bartpleiter/FPGC5/PCB/FPGC5IOboard/mini-din-6p-1.snapshot.2/Mini-DIN-6P.png

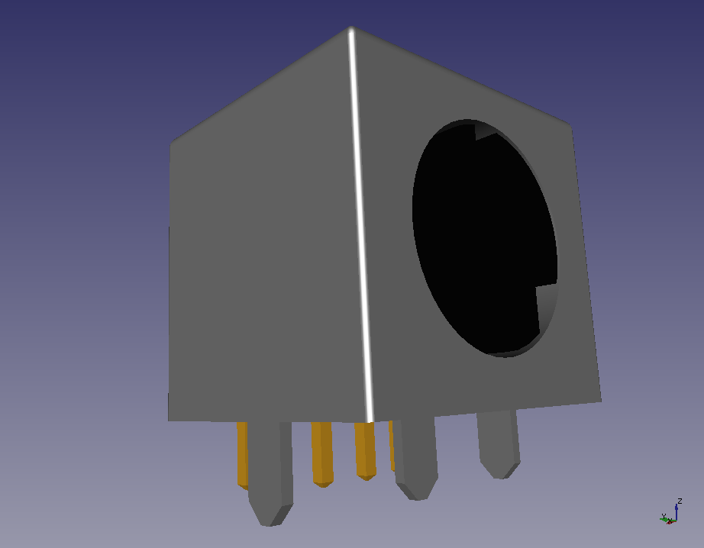
PCB/FPGC5IOboard/mini-din-6p-1.snapshot.2/Mini-DIN-6P.png
