bartpleiter/FPGC5/PCB/FPGC5IOboard/renders/FPGC4IOboardV2Bottom.png

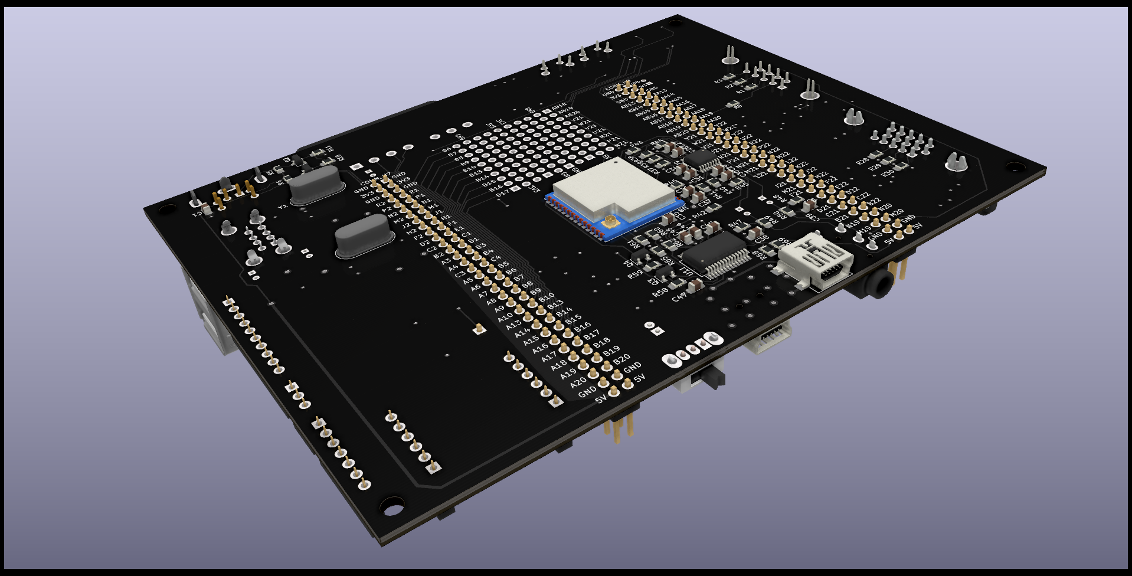
PCB/FPGC5IOboard/renders/FPGC4IOboardV2Bottom.png
