bartpleiter/FPGC5/PCB/FPGC5IOboard/renders/FPGC4IOboardV2BottomCloseUp.png

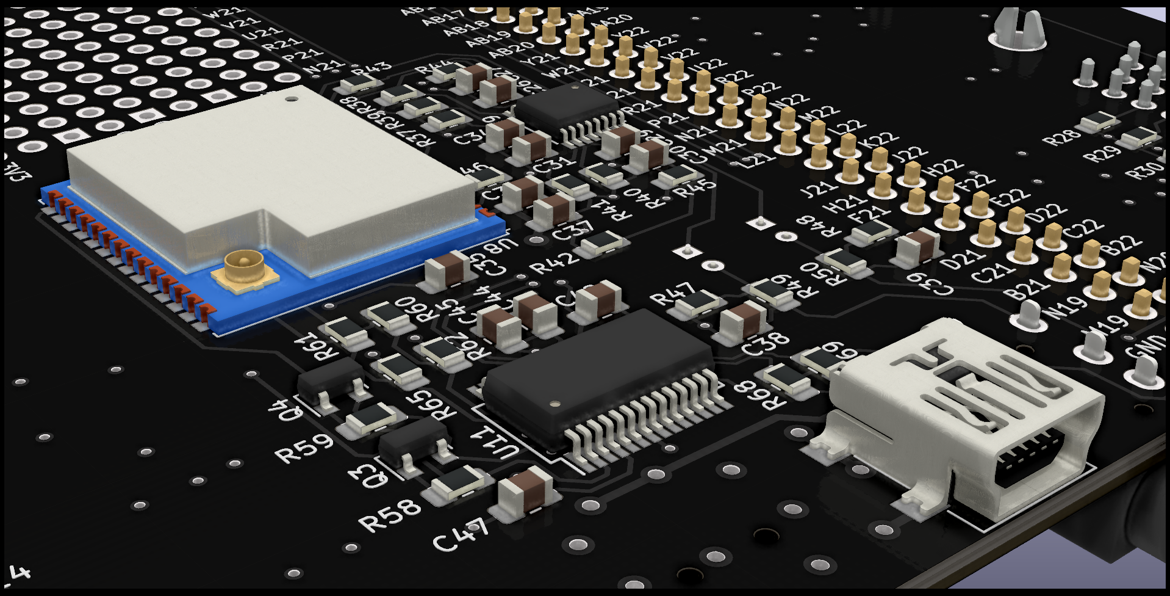
PCB/FPGC5IOboard/renders/FPGC4IOboardV2BottomCloseUp.png
