bartpleiter/FPGC5/PCB/FPGC5IOboard/renders/FPGC4IOboardV2FrontCloseUp.png

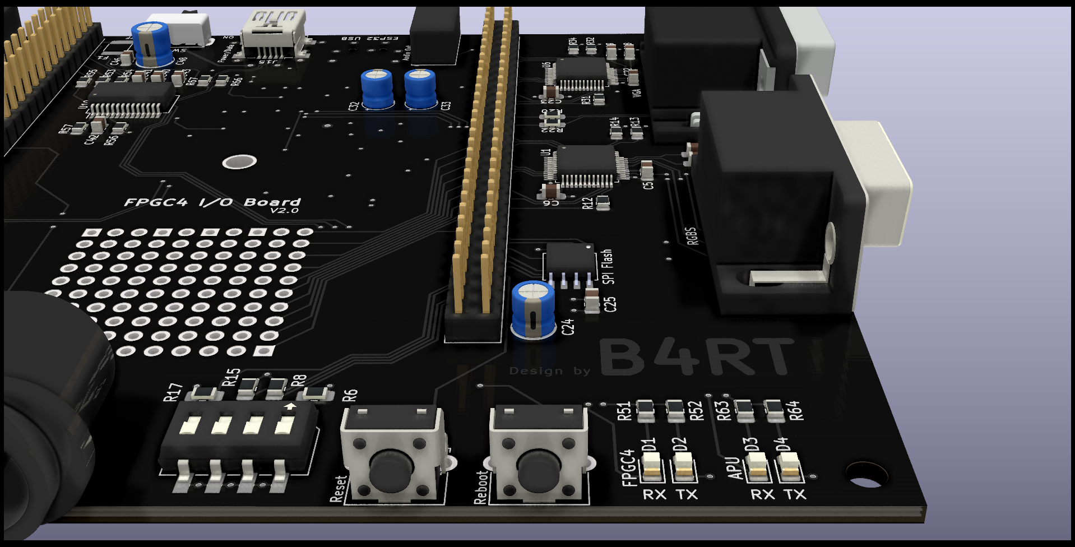
PCB/FPGC5IOboard/renders/FPGC4IOboardV2FrontCloseUp.png
