bartpleiter/FPGC5/PCB/FPGC5IOboard/renders/FPGC4IOboardV2Top.png

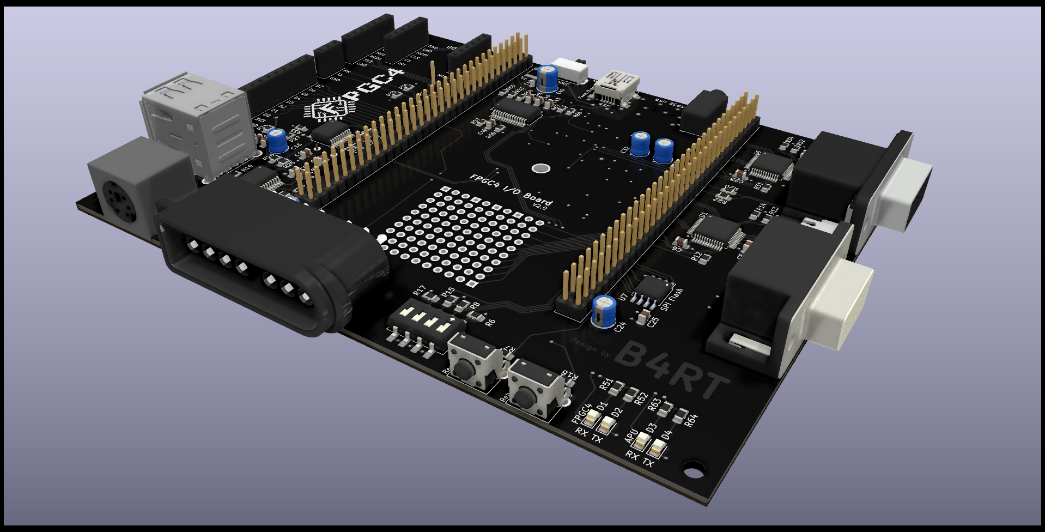
PCB/FPGC5IOboard/renders/FPGC4IOboardV2Top.png
