bartpleiter/FPGC5/PCB/FPGC5IOboard/3.5mm3D/FC68128.step

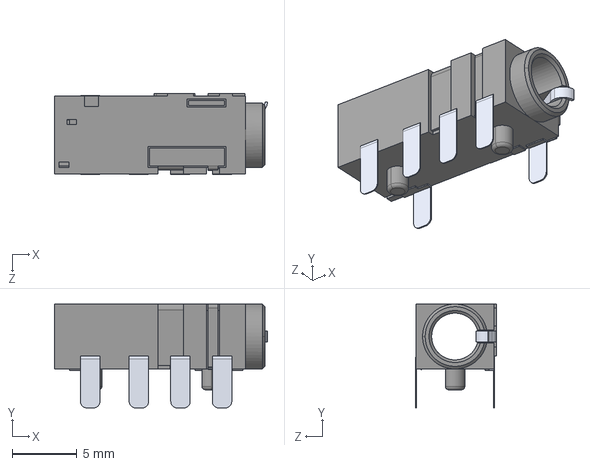
[picture p31: CAD file, 2021-06-23]
PCB/FPGC5IOboard/3.5mm3D/FC68128.step
16.4 x 8.00 x 6.25 mm
