bartpleiter/FPGC5/BCC/bcc.c

/*
Copyright (c) 2021, b4rt-dev
Copyright (c) 2012-2020, Alexey Frunze
All rights reserved.

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
1. Redistributions of source code must retain the above copyright notice, this
   list of conditions and the following disclaimer.
2. Redistributions in binary form must reproduce the above copyright notice,
   this list of conditions and the following disclaimer in the documentation
   and/or other materials provided with the distribution.

THIS SOFTWARE IS PROVIDED BY THE COPYRIGHT HOLDERS AND CONTRIBUTORS "AS IS" AND
ANY EXPRESS OR IMPLIED WARRANTIES, INCLUDING, BUT NOT LIMITED TO, THE IMPLIED
WARRANTIES OF MERCHANTABILITY AND FITNESS FOR A PARTICULAR PURPOSE ARE
DISCLAIMED. IN NO EVENT SHALL THE COPYRIGHT OWNER OR CONTRIBUTORS BE LIABLE FOR
ANY DIRECT, INDIRECT, INCIDENTAL, SPECIAL, EXEMPLARY, OR CONSEQUENTIAL DAMAGES
(INCLUDING, BUT NOT LIMITED TO, PROCUREMENT OF SUBSTITUTE GOODS OR SERVICES;
LOSS OF USE, DATA, OR PROFITS; OR BUSINESS INTERRUPTION) HOWEVER CAUSED AND
ON ANY THEORY OF LIABILITY, WHETHER IN CONTRACT, STRICT LIABILITY, OR TORT
(INCLUDING NEGLIGENCE OR OTHERWISE) ARISING IN ANY WAY OUT OF THE USE OF THIS
SOFTWARE, EVEN IF ADVISED OF THE POSSIBILITY OF SUCH DAMAGE.
*/

/*****************************************************************************/
/*                                                                           */
/*                           BCC (B322 C Compiler)                           */
/*                                                                           */
/*                           C compiler for B322                             */
/*                                                                           */
/*                            Based on SmallerC:                             */
/*                 A simple and small single-pass C compiler                 */
/*                                                                           */
/*                                Main file                                  */
/*                                                                           */
/*****************************************************************************/

// NOTE: still has a lot of extras in it that are not needed
//  only the "MIPS" part is needed with no extras

// Making most functions static helps with code optimization,
// use that to further reduce compiler's code size on RetroBSD.
#ifndef STATIC
#define STATIC
#else
#undef STATIC
#define STATIC static
#endif

#define NO_EXTRAS
#define CAN_COMPILE_32BIT
#define MIPS
#define B322

#ifdef NO_EXTRAS
#define NO_PPACK
#define NO_TYPEDEF_ENUM
#define NO_FUNC_
#define NO_EXTRA_WARNS
#define NO_FOR_DECL
#define NO_STRUCT_BY_VAL
#define NO_FP
#define NO_WCHAR
#endif

#ifndef __SMALLER_C__

//#include <limits.h>
#define CHAR_BIT        8
#define UINT_MAX        4294967295U
#define INT_MIN         -2147483648

//#include <ctype.h>
// isalpha
// isalnum
// isdigit

//#include <string.h>
// memmove
// strchr
// strcat
// strlen
// memcpy
// strncmp

#include <stdarg.h> // only used for printf related stuff and warnings/errors. Should be able to remove by replacing ALL(...) occurrences with a normal print function
#include <stdlib.h>
#include <stdio.h> // I/O functions

//#if UINT_MAX >= 0xFFFFFFFF
//#define CAN_COMPILE_32BIT
//#endif

#else // #ifndef __SMALLER_C__

#define NULL 0
#define size_t unsigned int

#define CHAR_BIT (8)

#ifdef __SMALLER_C_SCHAR__
#define CHAR_MIN (-128)
#define CHAR_MAX (127)
#endif
#ifdef __SMALLER_C_UCHAR__
#define CHAR_MIN (0)
#define CHAR_MAX (255)
#endif

#ifndef __SMALLER_C_SCHAR__
#ifndef __SMALLER_C_UCHAR__
#error __SMALLER_C_SCHAR__ or __SMALLER_C_UCHAR__ must be defined
#endif
#endif

#ifdef __SMALLER_C_16__
#define INT_MAX (32767)
#define INT_MIN (-32767-1)
#define UINT_MAX (65535u)
#define UINT_MIN (0u)
#endif
#ifdef __SMALLER_C_32__
#define INT_MAX (2147483647)
#define INT_MIN (-2147483647-1)
#define UINT_MAX (4294967295u)
#define UINT_MIN (0u)
//#define CAN_COMPILE_32BIT
#endif

#ifndef __SMALLER_C_16__
#ifndef __SMALLER_C_32__
#error __SMALLER_C_16__ or __SMALLER_C_32__ must be defined
#endif
#endif

#define EXIT_FAILURE 1

void exit(int);
int atoi(char*);

size_t strlen(char*);
char* strcpy(char*, char*);
char* strchr(char*, int);
int strcmp(char*, char*);
int strncmp(char*, char*, size_t);
void* memmove(void*, void*, size_t);
void* memcpy(void*, void*, size_t);
void* memset(void*, int, size_t);
int memcmp(void*, void*, size_t);

int isspace(int);
int isdigit(int);
int isalpha(int);
int isalnum(int);

#define FILE void
#define EOF (-1)
FILE* fopen(char*, char*);
int fclose(FILE*);
int putchar(int);
int fputc(int, FILE*);
int fgetc(FILE*);
int puts(char*);
int fputs(char*, FILE*);
int sprintf(char*, char*, ...);
//int vsprintf(char*, char*, va_list);
int vsprintf(char*, char*, void*);
int printf(char*, ...);
int fprintf(FILE*, char*, ...);
//int vprintf(char*, va_list);
int vprintf(char*, void*);
//int vfprintf(FILE*, char*, va_list);
int vfprintf(FILE*, char*, void*);
struct fpos_t_
{
  union
  {
    unsigned short halves[2]; // for 16-bit memory models without 32-bit longs
    int align; // for alignment on machine word boundary
  } u;
}; // keep in sync with stdio.h !!!
#define fpos_t struct fpos_t_
int fgetpos(FILE*, fpos_t*);
int fsetpos(FILE*, fpos_t*);

#endif // #ifndef __SMALLER_C__

// Floating point requires 32 bits
#ifndef CAN_COMPILE_32BIT
#ifndef NO_FP
#define NO_FP
#endif
#endif

////////////////////////////////////////////////////////////////////////////////

// all public macros

#ifndef MAX_IDENT_LEN
#define MAX_IDENT_LEN        63
#endif

#ifndef MAX_STRING_LEN
#define MAX_STRING_LEN       255
#endif
#define MAX_CHAR_QUEUE_LEN   (MAX_STRING_LEN + 1)

#ifndef MAX_MACRO_TABLE_LEN
#define MAX_MACRO_TABLE_LEN  (8192+1024)
#endif

#ifndef MAX_IDENT_TABLE_LEN
#define MAX_IDENT_TABLE_LEN  (8192+1024+512) // must be greater than MAX_IDENT_LEN
#endif

#ifndef SYNTAX_STACK_MAX
#define SYNTAX_STACK_MAX (4096+1024)
#endif

#ifndef MAX_FILE_NAME_LEN
#define MAX_FILE_NAME_LEN    95
#endif

#ifndef NO_PREPROCESSOR
#define MAX_INCLUDES         8
#define PREP_STACK_SIZE      8
#define MAX_SEARCH_PATH      256
#else
#define MAX_INCLUDES         1
#define PREP_STACK_SIZE      1
#define MAX_SEARCH_PATH      1
#undef MAX_STRING_LEN
#define MAX_STRING_LEN       (MAX_FILE_NAME_LEN + 3)
#endif

/* +-~* /% &|^! << >> && || < <= > >= == !=  () *[] ++ -- = += -= ~= *= /= %= &= |= ^= <<= >>= {} ,;: -> ... */

#define tokEof        0
#define tokNumInt     1
#define tokNumUint    2
#define tokLitStr     3

#define tokLShift     4
#define tokRShift     5
#define tokLogAnd     6
#define tokLogOr      7
#define tokEQ         8
#define tokNEQ        9
#define tokLEQ        10
#define tokGEQ        11
#define tokInc        12
#define tokDec        13
#define tokArrow      14
#define tokEllipsis   15

#define tokIdent      16
#define tokVoid       17
#define tokChar       18
#define tokInt        19
#define tokReturn     20
#define tokGoto       21
#define tokIf         22
#define tokElse       23
#define tokWhile      24
#define tokCont       25
#define tokBreak      26
#define tokSizeof     27

#define tokAssignMul  'A'
#define tokAssignDiv  'B'
#define tokAssignMod  'C'
#define tokAssignAdd  'D'
#define tokAssignSub  'E'
#define tokAssignLSh  'F'
#define tokAssignRSh  'G'
#define tokAssignAnd  'H'
#define tokAssignXor  'I'
#define tokAssignOr   'J'

#define tokFloat      'a'
#define tokDouble     'b'
#define tokLong       'c'
#define tokShort      'd'
#define tokUnsigned   'e'
#define tokSigned     'f'
#define tokConst      'g'
#define tokVolatile   'h'
#define tokRestrict   'i'
#define tokStatic     'j'
#define tokInline     'k'
#define tokExtern     'l'
#define tokAuto       'm'
#define tokRegister   'n'
#define tokTypedef    'o'
#define tokEnum       'p'
#define tokStruct     'q'
#define tokUnion      'r'
#define tokDo         's'
#define tokFor        't'
#define tokSwitch     'u'
#define tokCase       'v'
#define tokDefault    'w'
#define tok_Bool      'x'
#define tok_Complex   'y'
#define tok_Imagin    'z'

#define tok_Asm       '`'

/* Pseudo-tokens (converted from others or generated) */
#define tokURShift    28
#define tokUDiv       29
#define tokUMod       30
#define tokAssignURSh 31
#define tokAssignUDiv '@'
#define tokAssignUMod 'K'
#define tokComma      '0'

#define tokIfNot      'L'

#define tokUnaryAnd   'M'
#define tokUnaryStar  'N'
#define tokUnaryPlus  'O'
#define tokUnaryMinus 'P'

#define tokPostInc    'Q'
#define tokPostDec    'R'
#define tokPostAdd    'S'
#define tokPostSub    'T'

#define tokULess      'U'
#define tokUGreater   'V'
#define tokULEQ       'W'
#define tokUGEQ       'X'

#define tokLocalOfs   'Y'
#define tokShortCirc  'Z'

#define tokSChar      0x80
#define tokUChar      0x81
#define tokUShort     0x82
#define tokULong      0x83
//#define tokLongLong   0x84
//#define tokULongLong  0x85
//#define tokLongDbl    0x86
#define tokGotoLabel  0x8F
#define tokStructPtr  0x90
#define tokTag        0x91
#define tokMemberIdent 0x92
#define tokEnumPtr    0x93
#define tokIntr       0x94
#define tokNumFloat   0x95
#define tokNumCharWide 0x96
#define tokLitStrWide 0x97

//#define FormatFlat      0
#define FormatSegmented 1
//#define FormatSegTurbo  2
#define FormatSegHuge   3
#define FormatSegUnreal 4

#define SymVoidSynPtr 0
#define SymIntSynPtr  1
#define SymUintSynPtr 2
#define SymWideCharSynPtr 3
#define SymFloatSynPtr 4
#define SymFuncPtr    5

#ifndef STACK_SIZE
#define STACK_SIZE 129
#endif

#define SymFxn       1
#define SymGlobalVar 2
#define SymGlobalArr 3
#define SymLocalVar  4
#define SymLocalArr  5

// Division and Modulo without / and %
STATIC
int divmod(int dividend, int divisor, int* rem)
{
    int quotient = 1;

    int neg = 1;
    if ((dividend>0 &&divisor<0)||(dividend<0 && divisor>0))
        neg = -1;

    // Convert to positive
    int tempdividend = (dividend < 0) ? -dividend : dividend;
    int tempdivisor = (divisor < 0) ? -divisor : divisor;

    if (tempdivisor == tempdividend) {
        *rem = 0;
        return 1*neg;
    }
    else if (tempdividend < tempdivisor) {
        if (dividend < 0)
            *rem = tempdividend*neg;
        else
            *rem = tempdividend;
        return 0;
    }
    while (tempdivisor<<1 <= tempdividend)
    {
        tempdivisor = tempdivisor << 1;
        quotient = quotient << 1;
    }

    // Call division recursively
    if(dividend < 0)
        quotient = quotient*neg + divmod(-(tempdividend-tempdivisor), divisor, rem);
    else
        quotient = quotient*neg + divmod(tempdividend-tempdivisor, divisor, rem);
     return quotient;
}

STATIC
int division(int dividend, int divisor)
{
    int rem = 0;
    return divmod(dividend, divisor, &rem);
}

STATIC
int modulo(int dividend, int divisor)
{
    int rem = 0;
    divmod(dividend, divisor, &rem);
    return rem;
}


// isalpha
STATIC
int isalpha(int argument)
{
  if (argument >= 'A' && argument <= 'Z')
    return 2;
  if (argument >= 'a' && argument <= 'z')
    return 1;
  return 0;
}

// isdigit
STATIC
int isdigit(int argument)
{
  if (argument >= '0' && argument <= '9')
    return 1;
  return 0;
}

// isalnum
STATIC
int isalnum(int argument)
{
  if (isdigit(argument) || isalpha(argument))
    return 1;
  return 0;
}



STATIC
void* memcpy(void *dest, const void *src, size_t len)
{
   // Typecast src and dest addresses to (char *)
   char *csrc = (char *)src;
   char *cdest = (char *)dest;
  
   // Copy contents of src[] to dest[]
   int i;
   for (i=0; i<len; i++)
       cdest[i] = csrc[i];
}

STATIC
void* memmove(void* dest, const void* src, size_t n)
{
  unsigned char* from = (unsigned char*) src;
  unsigned char* to = (unsigned char*) dest;

  if (from == to || n == 0)
    return dest;
  if (to > from && to-from < (int)n) {
    /* to overlaps with from */
    /*  <from......>         */
    /*         <to........>  */
    /* copy in reverse, to avoid overwriting from */
    int i;
    for(i=n-1; i>=0; i--)
      to[i] = from[i];
    return dest;
  }
  if (from > to && from-to < (int)n) {
    /* to overlaps with from */
    /*        <from......>   */
    /*  <to........>         */
    /* copy forwards, to avoid overwriting from */
    size_t i;
    for(i=0; i<n; i++)
      to[i] = from[i];
    return dest;
  }
  memcpy(dest, src, n);
  return dest;
}

// Function to implement `strcpy()` function
STATIC
char* strcpy(char* destination, const char* source)
{
    // return if no memory is allocated to the destination
    if (destination == NULL) {
        return NULL;
    }
 
    // take a pointer pointing to the beginning of the destination string
    char *ptr = destination;
 
    // copy the C-string pointed by source into the array
    // pointed by destination
    while (*source != '\0')
    {
        *destination = *source;
        destination++;
        source++;
    }
 
    // include the terminating null character
    *destination = '\0';
 
    // the destination is returned by standard `strcpy()`
    return ptr;
}


STATIC
size_t strlen(const char *str)
{
        const char *s;
        for (s = str; *s; ++s);
        return (s - str);
}

STATIC
char* strcat (char *dest, const char *src)
{
  strcpy (dest + strlen (dest), src);
  return dest;
}

STATIC
char* strchr (const char *s, int c)
{
  do {
    if (*s == c)
      {
        return (char*)s;
      }
  } while (*s++);
  return (0);
}


STATIC
int strcmp(const char* s1, const char* s2)
{
  while(*s1 && (*s1 == *s2))
  {
    s1++;
    s2++;
  }
  return *(unsigned char*)s1 - *(unsigned char*)s2;
}

//STATIC

int strncmp(const char * s1, const char * s2, size_t n )
{
  while ( n && *s1 && ( *s1 == *s2 ) )
  {
    ++s1;
    ++s2;
    --n;
  }
  if ( n == 0 )
  {
    return 0;
  }
  else
  {
    return ( *(unsigned char *)s1 - *(unsigned char *)s2 );
  }
}



// all public prototypes
STATIC
unsigned truncUint(unsigned);
STATIC
int truncInt(int);

STATIC
int GetToken(void);
STATIC
char* GetTokenName(int token);

#ifndef NO_PREPROCESSOR
#ifndef NO_ANNOTATIONS
STATIC
void DumpMacroTable(void);
#endif
#endif

STATIC
int AddIdent(char* name);
STATIC
int FindIdent(char* name);
#ifndef NO_ANNOTATIONS
STATIC
void DumpIdentTable(void);
#endif
STATIC
char* lab2str(char* p, int n);

STATIC
void GenInit(void);
STATIC
void GenFin(void);
STATIC
int GenInitParams(int argc, char** argv, int* idx);
STATIC
void GenInitFinalize(void);
STATIC
void GenStartCommentLine(void);
STATIC
void GenWordAlignment(int bss);
STATIC
void GenLabel(char* Label, int Static);
STATIC
void GenNumLabel(int Label);
STATIC
void GenZeroData(unsigned Size, int bss);
STATIC
void GenIntData(int Size, int Val);
STATIC
void GenStartAsciiString(void);
STATIC
void GenAddrData(int Size, char* Label, int ofs);

STATIC
void GenJumpUncond(int Label);
STATIC
void GenJumpIfZero(int Label);
STATIC
void GenJumpIfNotZero(int Label);
STATIC
void GenJumpIfEqual(int val, int Label);

STATIC
void GenFxnProlog(void);
STATIC
void GenFxnEpilog(void);
void GenIsrProlog(void);
void GenIsrEpilog(void);

STATIC
int GenMaxLocalsSize(void);

STATIC
void GenDumpChar(int ch);
STATIC
void GenExpr(void);

STATIC
void PushSyntax(int t);
STATIC
void PushSyntax2(int t, int v);

#ifndef NO_ANNOTATIONS
STATIC
void DumpSynDecls(void);
#endif

STATIC
void push2(int v, int v2);
STATIC
void ins2(int pos, int v, int v2);
STATIC
void ins(int pos, int v);
STATIC
void del(int pos, int cnt);

STATIC
int TokenStartsDeclaration(int t, int params);
STATIC
int ParseDecl(int tok, unsigned structInfo[4], int cast, int label);

STATIC
void ShiftChar(void);
STATIC
int puts2(char*);
STATIC
int printf2(char*, ...);

STATIC
void error(char* format, ...);
STATIC
void warning(char* format, ...);
STATIC
void errorFile(char* n);
STATIC
void errorFileName(void);
STATIC
void errorInternal(int n);
STATIC
void errorChrStr(void);
#ifndef NO_WCHAR
STATIC
void errorWideNonWide(void);
#endif
STATIC
void errorStrLen(void);
STATIC
void errorUnexpectedToken(int tok);
STATIC
void errorDirective(void);
STATIC
void errorCtrlOutOfScope(void);
STATIC
void errorDecl(void);
STATIC
void errorVarSize(void);
STATIC
void errorInit(void);
STATIC
void errorUnexpectedVoid(void);
STATIC
void errorOpType(void);
STATIC
void errorNotLvalue(void);
STATIC
void errorNotConst(void);
STATIC
void errorLongExpr(void);
#ifndef NO_FP
STATIC
void warnFloat2Int(void);
#endif

STATIC
int FindSymbol(char* s);
STATIC
int SymType(int SynPtr);
STATIC
int FindTaggedDecl(char* s, int start, int* CurScope);
#ifndef NO_TYPEDEF_ENUM
STATIC
int FindTypedef(char* s);
#endif
STATIC
int GetDeclSize(int SyntaxPtr, int SizeForDeref);

STATIC
int ParseExpr(int tok, int* GotUnary, int* ExprTypeSynPtr, int* ConstExpr, int* ConstVal, int option, int option2);
STATIC
int GetFxnInfo(int ExprTypeSynPtr, int* MinParams, int* MaxParams, int* ReturnExprTypeSynPtr, int* FirstParamSynPtr);

// all data

int verbose = 0;
int warnings = 0;
int warnCnt = 0;

// custom compiler flags
int compileUserBDOS = 0;
int compileOS = 0;

// prep.c data

// TBD!!! get rid of TokenIdentName[] and TokenValueString[]
// and work with CharQueue[] directly
int TokenValueInt = 0;
char TokenIdentName[MAX_IDENT_LEN + 1];
int TokenIdentNameLen = 0;
char TokenValueString[MAX_STRING_LEN + 1];
unsigned TokenStringLen = 0;
unsigned TokenStringSize = 0; // TokenStringLen * sizeof(char/wchar_t)
int LineNo = 1;
int LinePos = 1;
char CharQueue[MAX_CHAR_QUEUE_LEN];
int CharQueueLen = 0;

#ifndef NO_PREPROCESSOR
/*
  Macro table entry format:
    idlen char:     identifier length (<= 127)
    id char[idlen]: identifier (ASCIIZ)
    exlen char:     length of what the identifier expands into (<= 127)
    ex char[exlen]: what the identifier expands into (ASCII)
*/
char MacroTable[MAX_MACRO_TABLE_LEN];
int MacroTableLen = 0;
#endif

/*
  Identifier table entry format:
    id char[idlen]: string (ASCIIZ)
    idlen char:     string length (<= 127)
*/
char IdentTable[MAX_IDENT_TABLE_LEN];
int IdentTableLen = 0;
int DummyIdent; // corresponds to empty string

#ifndef MAX_GOTO_LABELS
#define MAX_GOTO_LABELS 16
#endif
int gotoLabels[MAX_GOTO_LABELS][2];
// gotoLabStat[]: bit 1 = used (by "goto label;"), bit 0 = defined (with "label:")
char gotoLabStat[MAX_GOTO_LABELS];
int gotoLabCnt = 0;

#ifndef MAX_CASES
#define MAX_CASES 128
#endif
int Cases[MAX_CASES][2]; // [0] is case constant, [1] is case label number
int CasesCnt = 0;

// Data structures to support #include
int FileCnt = 0;
char FileNames[MAX_INCLUDES][MAX_FILE_NAME_LEN + 1];
FILE* Files[MAX_INCLUDES];
FILE* OutFile;
char CharQueues[MAX_INCLUDES][3];
int LineNos[MAX_INCLUDES];
int LinePoss[MAX_INCLUDES];
char SysSearchPaths[MAX_SEARCH_PATH];
int SysSearchPathsLen = 0;
char SearchPaths[MAX_SEARCH_PATH];
int SearchPathsLen = 0;

// Data structures to support #ifdef/#ifndef,#else,#endif
int PrepDontSkipTokens = 1;
int PrepStack[PREP_STACK_SIZE][2];
int PrepSp = 0;

// Data structures to support #pragma pack(...)
#ifndef NO_PPACK
#define PPACK_STACK_SIZE 16
int PragmaPackValue;
int PragmaPackValues[PPACK_STACK_SIZE];
int PragmaPackSp = 0;
#endif

// expr.c data

int ExprLevel = 0;

// TBD??? merge expression and operator stacks into one
int stack[STACK_SIZE][2];
int sp = 0;

#define OPERATOR_STACK_SIZE STACK_SIZE
int opstack[OPERATOR_STACK_SIZE][2];
int opsp = 0;

// smc.c data

int OutputFormat = FormatSegmented;
int GenExterns = 1;
int UseBss = 1;

// Names of C functions and variables are usually prefixed with an underscore.
// One notable exception is the ELF format used by gcc in Linux.
// Global C identifiers in the ELF format should not be predixed with an underscore.
int UseLeadingUnderscores = 1;

char* FileHeader = "";
char* CodeHeaderFooter[2] = { "", "" };
char* DataHeaderFooter[2] = { "", "" };
char* RoDataHeaderFooter[2] = { "", "" };
char* BssHeaderFooter[2] = { "", "" };
char** CurHeaderFooter;

int CharIsSigned = 1;
int SizeOfWord = 2; // in chars (char can be a multiple of octets); ints and pointers are of word size
int SizeOfWideChar = 2; // in chars/bytes, 2 or 4
int WideCharIsSigned = 0; // 0 or 1
int WideCharType1;
int WideCharType2; // (un)signed counterpart of WideCharType1

// TBD??? implement a function to allocate N labels with overflow checks
int LabelCnt = 1; // label counter for jumps
int StructCpyLabel = 0; // label of the function to copy structures/unions
int StructPushLabel = 0; // label of the function to push structures/unions onto the stack

// call stack (from higher to lower addresses):
//   arg n
//   ...
//   arg 1
//   return address
//   saved xbp register
//   local var 1
//   ...
//   local var n
int CurFxnSyntaxPtr = 0;
int CurFxnParamCntMin = 0;
int CurFxnParamCntMax = 0;
int CurFxnLocalOfs = 0; // negative
int CurFxnMinLocalOfs = 0; // negative

int CurFxnReturnExprTypeSynPtr = 0;
int CurFxnEpilogLabel = 0;

char* CurFxnName = NULL;
#ifndef NO_FUNC_
int CurFxnNameLabel = 0;
#endif
int IsMain; // if inside main()

int ParseLevel = 0; // Parse level/scope (file:0, fxn:1+)
int ParamLevel = 0; // 1+ if parsing params, 0 otherwise

unsigned char SyntaxStack0[SYNTAX_STACK_MAX];
int SyntaxStack1[SYNTAX_STACK_MAX];
int SyntaxStackCnt;

// all code

STATIC
unsigned truncUint(unsigned n)
{
  // Truncate n to SizeOfWord * 8 bits
  if (SizeOfWord == 2)
    n &= ~(~0u << 8 << 8);
#ifdef CAN_COMPILE_32BIT
  else if (SizeOfWord == 4)
    n &= ~(~0u << 8 << 12 << 12);
#endif
  return n;
}

STATIC
int truncInt(int n)
{
  // Truncate n to SizeOfWord * 8 bits and then sign-extend it
  unsigned un = n;
  if (SizeOfWord == 2)
  {
    un &= ~(~0u << 8 << 8);
    un |= (((un >> 8 >> 7) & 1) * ~0u) << 8 << 8;
  }
#ifdef CAN_COMPILE_32BIT
  else if (SizeOfWord == 4)
  {
    un &= ~(~0u << 8 << 12 << 12);
    un |= (((un >> 8 >> 12 >> 11) & 1) * ~0u) << 8 << 12 << 12;
  }
#endif
  return (int)un;
}

// prep.c code

#ifndef NO_PREPROCESSOR
STATIC
int FindMacro(char* name)
{
  int i;

  for (i = 0; i < MacroTableLen; )
  {
    if (!strcmp(MacroTable + i + 1, name))
      return i + 1 + MacroTable[i];

    i = i + 1 + MacroTable[i]; // skip id
    i = i + 1 + MacroTable[i]; // skip ex
  }

  return -1;
}

STATIC
int UndefineMacro(char* name)
{
  int i;

  for (i = 0; i < MacroTableLen; )
  {
    if (!strcmp(MacroTable + i + 1, name))
    {
      int len = 1 + MacroTable[i]; // id part len
      len = len + 1 + MacroTable[i + len]; // + ex part len

      memmove(MacroTable + i,
              MacroTable + i + len,
              MacroTableLen - i - len);
      MacroTableLen -= len;

      return 1;
    }

    i = i + 1 + MacroTable[i]; // skip id
    i = i + 1 + MacroTable[i]; // skip ex
  }

  return 0;
}

STATIC
void AddMacroIdent(char* name)
{
  int l = strlen(name);

  if (l >= 127)
    error("Macro identifier too long '%s'\n", name);

  if (MAX_MACRO_TABLE_LEN - MacroTableLen < l + 3)
    error("Macro table exhausted\n");

  MacroTable[MacroTableLen++] = l + 1; // idlen
  strcpy(MacroTable + MacroTableLen, name);
  MacroTableLen += l + 1;

  MacroTable[MacroTableLen] = 0; // exlen
}

STATIC
void AddMacroExpansionChar(char e)
{
  if (e == '\0')
  {
    // finalize macro definition entry
    // remove trailing space first
    while (MacroTable[MacroTableLen] &&
           strchr(" \t", MacroTable[MacroTableLen + MacroTable[MacroTableLen]]))
      MacroTable[MacroTableLen]--;
    MacroTableLen += 1 + MacroTable[MacroTableLen];
    return;
  }

  if (MacroTableLen + 1 + MacroTable[MacroTableLen] >= MAX_MACRO_TABLE_LEN)
    error("Macro table exhausted\n");

  if (MacroTable[MacroTableLen] >= 127)
    error("Macro definition too long\n");

  MacroTable[MacroTableLen + 1 + MacroTable[MacroTableLen]] = e;
  MacroTable[MacroTableLen]++;
}

STATIC
void DefineMacro(char* name, char* expansion)
{
  AddMacroIdent(name);
  do
  {
    AddMacroExpansionChar(*expansion);
  } while (*expansion++ != '\0');
}

#ifndef NO_ANNOTATIONS
STATIC
void DumpMacroTable(void)
{
  int i, j;

  puts2("");
  GenStartCommentLine(); printf2("Macro table:\n");
  for (i = 0; i < MacroTableLen; )
  {
    GenStartCommentLine(); printf2("Macro %s = ", MacroTable + i + 1);
    i = i + 1 + MacroTable[i]; // skip id
    printf2("`");
    j = MacroTable[i++];
    while (j--)
      printf2("%c", MacroTable[i++]);
    printf2("`\n");
  }
  GenStartCommentLine(); printf2("Bytes used: %d/%d\n\n", MacroTableLen, MAX_MACRO_TABLE_LEN);
}
#endif
#endif // #ifndef NO_PREPROCESSOR

STATIC
int FindIdent(char* name)
{
  int i;
  for (i = IdentTableLen; i > 0; )
  {
    i -= 1 + IdentTable[i - 1];
    if (!strcmp(IdentTable + i, name))
      return i;
  }
  return -1;
}

STATIC
int AddIdent(char* name)
{
  int i, len;

  if ((i = FindIdent(name)) >= 0)
    return i;

  i = IdentTableLen;
  len = strlen(name);

  if (len >= 127)
    error("Identifier too long\n");

  if (MAX_IDENT_TABLE_LEN - IdentTableLen < len + 2)
    error("Identifier table exhausted\n");

  strcpy(IdentTable + IdentTableLen, name);
  IdentTableLen += len + 1;
  IdentTable[IdentTableLen++] = len + 1;

  return i;
}

STATIC
int AddNumericIdent(int n)
{
  char s[1 + (2 + CHAR_BIT * sizeof n) / 3];
  char *p = s + sizeof s;
  *--p = '\0';
  p = lab2str(p, n);
  return AddIdent(p);
}

STATIC
int AddGotoLabel(char* name, int label)
{
  int i;
  for (i = 0; i < gotoLabCnt; i++)
  {
    if (!strcmp(IdentTable + gotoLabels[i][0], name))
    {
      if (gotoLabStat[i] & label)
        error("Redefinition of label '%s'\n", name);
      gotoLabStat[i] |= 2*!label + label;
      return gotoLabels[i][1];
    }
  }
  if (gotoLabCnt >= MAX_GOTO_LABELS)
    error("Goto table exhausted\n");
  gotoLabels[gotoLabCnt][0] = AddIdent(name);
  gotoLabels[gotoLabCnt][1] = LabelCnt++;
  gotoLabStat[gotoLabCnt] = 2*!label + label;
  return gotoLabels[gotoLabCnt++][1];
}

STATIC
void UndoNonLabelIdents(int len)
{
  int i;
  IdentTableLen = len;
  for (i = 0; i < gotoLabCnt; i++)
    if (gotoLabels[i][0] >= len)
    {
      char* pfrom = IdentTable + gotoLabels[i][0];
      char* pto = IdentTable + IdentTableLen;
      int l = strlen(pfrom) + 2;
      memmove(pto, pfrom, l);
      IdentTableLen += l;
      gotoLabels[i][0] = pto - IdentTable;
    }
}

STATIC
void AddCase(int val, int label)
{
  if (CasesCnt >= MAX_CASES)
    error("Case table exhausted\n");

  Cases[CasesCnt][0] = val;
  Cases[CasesCnt++][1] = label;
}

#ifndef NO_ANNOTATIONS
STATIC
void DumpIdentTable(void)
{
  int i;
  puts2("");
  GenStartCommentLine(); printf2("Identifier table:\n");
  for (i = 0; i < IdentTableLen; )
  {
    GenStartCommentLine(); printf2("Ident %s\n", IdentTable + i);
    i += strlen(IdentTable + i) + 2;
  }
  GenStartCommentLine(); printf2("Bytes used: %d/%d\n\n", IdentTableLen, MAX_IDENT_TABLE_LEN);
}
#endif

char* rws[] =
{
  "break", "case", "char", "continue", "default", "do", "else",
  "extern", "for", "if", "int", "return", "signed", "sizeof",
  "static", "switch", "unsigned", "void", "while", "asm", "auto",
  "const", "double", "enum", "float", "goto", "inline", "long",
  "register", "restrict", "short", "struct", "typedef", "union",
  "volatile", "_Bool", "_Complex", "_Imaginary",
  "__interrupt"
};

unsigned char rwtk[] =
{
  tokBreak, tokCase, tokChar, tokCont, tokDefault, tokDo, tokElse,
  tokExtern, tokFor, tokIf, tokInt, tokReturn, tokSigned, tokSizeof,
  tokStatic, tokSwitch, tokUnsigned, tokVoid, tokWhile, tok_Asm, tokAuto,
  tokConst, tokDouble, tokEnum, tokFloat, tokGoto, tokInline, tokLong,
  tokRegister, tokRestrict, tokShort, tokStruct, tokTypedef, tokUnion,
  tokVolatile, tok_Bool, tok_Complex, tok_Imagin,
  tokIntr
};

STATIC
int GetTokenByWord(char* word)
{
  unsigned i;

  for (i = 0; i < division(sizeof rws, sizeof rws[0]); i++)
    if (!strcmp(rws[i], word))
      return rwtk[i];

  return tokIdent;
}

unsigned char tktk[] =
{
  tokEof,
  // Single-character operators and punctuators:
  '+', '-', '~', '*', '/', '%', '&', '|', '^', '!',
  '<', '>', '(', ')', '[', ']',
  '{', '}', '=', ',', ';', ':', '.', '?',
  // Multi-character operators and punctuators:
  tokLShift, tokLogAnd, tokEQ, tokLEQ, tokInc, tokArrow, tokAssignMul,
  tokAssignMod, tokAssignSub, tokAssignRSh, tokAssignXor,
  tokRShift, tokLogOr, tokNEQ, tokGEQ, tokDec, tokEllipsis,
  tokAssignDiv, tokAssignAdd, tokAssignLSh, tokAssignAnd, tokAssignOr,
  // Some of the above tokens get converted into these in the process:
  tokUnaryAnd, tokUnaryPlus, tokPostInc, tokPostAdd,
  tokULess, tokULEQ, tokURShift, tokUDiv, tokUMod, tokComma,
  tokUnaryStar, tokUnaryMinus, tokPostDec, tokPostSub,
  tokUGreater, tokUGEQ, tokAssignURSh, tokAssignUDiv, tokAssignUMod,
  // Helper (pseudo-)tokens:
  tokNumInt, tokLitStr, tokLocalOfs, tokNumUint, tokIdent, tokShortCirc,
  tokSChar, tokShort, tokLong, tokUChar, tokUShort, tokULong, tokNumFloat,
  tokNumCharWide, tokLitStrWide
};

char* tks[] =
{
  "<EOF>",
  // Single-character operators and punctuators:
  "+", "-", "~", "*", "/", "%", "&", "|", "^", "!",
  "<", ">", "(", ")", "[", "]",
  "{", "}", "=", ",", ";", ":", ".", "?",
  // Multi-character operators and punctuators:
  "<<", "&&", "==", "<=", "++", "->", "*=",
  "%=", "-=", ">>=", "^=",
  ">>", "||", "!=", ">=", "--", "...",
  "/=", "+=", "<<=", "&=", "|=",
  // Some of the above tokens get converted into these in the process:
  "&u", "+u", "++p", "+=p",
  "<u", "<=u", ">>u", "/u", "%u", ",b",
  "*u", "-u", "--p", "-=p",
  ">u", ">=u", ">>=u", "/=u", "%=u",
  // Helper (pseudo-)tokens:
  "<NumInt>",  "<LitStr>", "<LocalOfs>", "<NumUint>", "<Ident>", "<ShortCirc>",
  "signed char", "short", "long", "unsigned char", "unsigned short", "unsigned long", "float",
  "<NumCharWide>", "<LitStrWide>"
};

STATIC
char* GetTokenName(int token)
{
  unsigned i;

/* +-~* /% &|^! << >> && || < <= > >= == !=  () *[] ++ -- = += -= ~= *= /= %= &= |= ^= <<= >>= {} ,;: -> ... */

  // Tokens other than reserved keywords:
  for (i = 0; i < division(sizeof tktk , sizeof tktk[0]); i++)
    if (tktk[i] == token)
      return tks[i];

  // Reserved keywords:
  for (i = 0; i < division(sizeof rws , sizeof rws[0]); i++)
    if (rwtk[i] == token)
      return rws[i];

  //error("Internal Error: GetTokenName(): Invalid token %d\n", token);
  errorInternal(1);
  return "";
}

STATIC
int GetNextChar(void)
{
  int ch = EOF;

  if (FileCnt && Files[FileCnt - 1])
  {
    if ((ch = fgetc(Files[FileCnt - 1])) == EOF)
    {
      fclose(Files[FileCnt - 1]);
      Files[FileCnt - 1] = NULL;

      // store the last line/pos, they may still be needed later
      LineNos[FileCnt - 1] = LineNo;
      LinePoss[FileCnt - 1] = LinePos;

      // don't drop the file record just yet
    }
  }

  return ch;
}

STATIC
void ShiftChar(void)
{
  if (CharQueueLen)
    memmove(CharQueue, CharQueue + 1, --CharQueueLen);

  // make sure there always are at least 3 chars in the queue
  while (CharQueueLen < 3)
  {
    int ch = GetNextChar();
    if (ch == EOF)
      ch = '\0';
    CharQueue[CharQueueLen++] = ch;
  }
}

STATIC
void ShiftCharN(int n)
{
  while (n-- > 0)
  {
    ShiftChar();
    LinePos++;
  }
}

#ifndef NO_PREPROCESSOR
STATIC
void IncludeFile(int quot)
{
  int nlen = strlen(TokenValueString);

  if (CharQueueLen != 3)
    //error("#include parsing error\n");
    errorInternal(2);

  if (FileCnt >= MAX_INCLUDES)
    error("Too many include files\n");

  // store the including file's position and buffered chars
  LineNos[FileCnt - 1] = LineNo;
  LinePoss[FileCnt - 1] = LinePos;
  memcpy(CharQueues[FileCnt - 1], CharQueue, CharQueueLen);

  // open the included file

  if (nlen > MAX_FILE_NAME_LEN)
    //error("File name too long\n");
    errorFileName();

  // DONE: differentiate between quot == '"' and quot == '<'

  // First, try opening "file" in the current directory
  // (Open Watcom C/C++ 1.9, Turbo C++ 1.01 use the current directory,
  // unlike gcc, which uses the same directory as the current file)
  if (quot == '"')
  {
    // Get path from c file to compile, so it can be appended to the include paths
    char cFileDir[255] = "";
    strcpy(cFileDir, FileNames[0]);

    int len = strlen(cFileDir);  
    while (len > 0) 
    {
       len--;
       if (cFileDir[len] == '/') 
       {
          cFileDir[len+1] = '\0'; // keep the slash
          break;
       }
    }
    if (len == 0) // remove directory if there is none
    {
      cFileDir[0] = '\0';
    }
    strcpy(FileNames[FileCnt], TokenValueString);
    strcat(cFileDir, FileNames[FileCnt]);
    Files[FileCnt] = fopen(cFileDir, "r");
  }

  // Next, iterate the search paths trying to open "file" or <file>.
  // "file" is first searched using the list provided by the -I option.
  // "file" is then searched using the list provided by the -SI option.
  // <file> is searched using the list provided by the -SI option.
  if (Files[FileCnt] == NULL)
  {
    int i;
    char *paths = SearchPaths;
    int pl = SearchPathsLen;
    for (;;)
    {
      if (quot == '<')
      {
        paths = SysSearchPaths;
        pl = SysSearchPathsLen;
      }
      for (i = 0; i < pl; )
      {
        int plen = strlen(paths + i);
        if (plen + 1 + nlen < MAX_FILE_NAME_LEN)
        {
          strcpy(FileNames[FileCnt], paths + i);
          strcpy(FileNames[FileCnt] + plen + 1, TokenValueString);
          // Use '/' as a separator, typical for Linux/Unix,
          // but also supported by file APIs in DOS/Windows just as '\\'
          FileNames[FileCnt][plen] = '/';
          if ((Files[FileCnt] = fopen(FileNames[FileCnt], "r")) != NULL)
            break;
        }
        i += plen + 1;
      }
      if (Files[FileCnt] || quot == '<')
        break;
      quot = '<';
    }
  }

  if (Files[FileCnt] == NULL)
  {
    //error("Cannot open file \"%s\"\n", TokenValueString);
    errorFile(TokenValueString);
  }

  // reset line/pos and empty the char queue
  CharQueueLen = 0;
  LineNo = LinePos = 1;
  FileCnt++;

  // fill the char queue with file data
  ShiftChar();
}
#endif // #ifndef NO_PREPROCESSOR

STATIC
int EndOfFiles(void)
{
  // if there are no including files, we're done
  if (!--FileCnt)
    return 1;

  // restore the including file's position and buffered chars
  LineNo = LineNos[FileCnt - 1];
  LinePos = LinePoss[FileCnt - 1];
  CharQueueLen = 3;
  memcpy(CharQueue, CharQueues[FileCnt - 1], CharQueueLen);

  return 0;
}

STATIC
void SkipSpace(int SkipNewLines)
{
  char* p = CharQueue;

  while (*p != '\0')
  {
    if (strchr(" \t\f\v", *p))
    {
      ShiftCharN(1);
      continue;
    }

    if (strchr("\r\n", *p))
    {
      if (!SkipNewLines)
        return;

      if (*p == '\r' && p[1] == '\n')
        ShiftChar();

      ShiftChar();
      LineNo++;
      LinePos = 1;
      continue;
    }

#ifndef NO_PREPROCESSOR
    if (*p == '/')
    {
      if (p[1] == '/')
      {
        // // comment
        ShiftCharN(2);
        while (!strchr("\r\n", *p))
          ShiftCharN(1);
        continue;
      }
      else if (p[1] == '*')
      {
        // /**/ comment
        ShiftCharN(2);
        while (*p != '\0' && !(*p == '*' && p[1] == '/'))
        {
          if (strchr("\r\n", *p))
          {
            if (!SkipNewLines)
              error("Invalid comment\n");

            if (*p == '\r' && p[1] == '\n')
              ShiftChar();

            ShiftChar();
            LineNo++;
            LinePos = 1;
          }
          else
          {
            ShiftCharN(1);
          }
        }
        if (*p == '\0')
          error("Invalid comment\n");
        ShiftCharN(2);
        continue;
      }
    } // endof if (*p == '/')
#endif

    break;
  } // endof while (*p != '\0')
}

#ifndef NO_PREPROCESSOR
STATIC
void SkipLine(void)
{
  char* p = CharQueue;

  while (*p != '\0')
  {
    if (strchr("\r\n", *p))
    {
      if (*p == '\r' && p[1] == '\n')
        ShiftChar();

      ShiftChar();
      LineNo++;
      LinePos = 1;
      break;
    }
    else
    {
      ShiftCharN(1);
    }
  }
}
#endif

STATIC
void GetIdent(void)
{
  char* p = CharQueue;

  if (*p != '_' && !isalpha(*p & 0xFFu))
    error("Identifier expected\n");

#ifdef NO_WCHAR
  if (*p == 'L' &&
      (p[1] == '\'' || p[1] == '"'))
    //error("Wide characters and strings not supported\n");
    errorChrStr();
#endif

  TokenIdentNameLen = 0;
  TokenIdentName[TokenIdentNameLen++] = *p;
  TokenIdentName[TokenIdentNameLen] = '\0';
  ShiftCharN(1);

  while (*p == '_' || isalnum(*p & 0xFFu))
  {
    if (TokenIdentNameLen == MAX_IDENT_LEN)
      error("Identifier too long '%s'\n", TokenIdentName);
    TokenIdentName[TokenIdentNameLen++] = *p;
    TokenIdentName[TokenIdentNameLen] = '\0';
    ShiftCharN(1);
  }
}

STATIC
unsigned GetCharValue(int wide)
{
  char* p = CharQueue;
  unsigned ch = 0;
  int cnt = 0;
#ifdef NO_WCHAR
  (void)wide;
#endif
  if (*p == '\\')
  {
    ShiftCharN(1);
    if (strchr("\n\r", *p))
      goto lerr;
    if (*p == 'x')
    {
      // hexadecimal character codes \xN+
      // hexadecimal escape sequence is not limited in length per se
      // (may have many leading zeroes)
      static char digs[] = "0123456789ABCDEFabcdef";
      static char vals[] =
      {
        0, 1, 2, 3, 4, 5, 6, 7, 8, 9,
        10, 11, 12, 13, 14, 15,
        10, 11, 12, 13, 14, 15
      };
      char* pp;
      int zeroes = 0;
      ShiftCharN(1);
      if (strchr("\n\r", *p))
        goto lerr;
      if (*p == '0')
      {
        do
        {
          ShiftCharN(1);
        } while (*p == '0');
        zeroes = 1;
      }
      while (*p && (pp = strchr(digs, *p)) != NULL)
      {
        ch <<= 4;
        ch |= vals[pp - digs];
        ShiftCharN(1);
#ifndef NO_WCHAR
        if (++cnt > (wide ? SizeOfWideChar * 2 : 2))
#else
        if (++cnt > 2)
#endif
        {
          if (PrepDontSkipTokens)
            goto lerr;
        }
      }
      if (zeroes + cnt == 0)
        goto lerr;
    }
    else if (*p >= '0' && *p <= '7')
    {
      // octal character codes \N+
      // octal escape sequence is terminated after three octal digits
      do
      {
        ch <<= 3;
        ch |= *p - '0';
        ShiftCharN(1);
        ++cnt;
      } while (*p >= '0' && *p <= '7' && cnt < 3);
      if (ch >> 8)
        goto lerr;
    }
    else
    {
      switch (*p)
      {
      case 'a': ch = '\a'; ShiftCharN(1); break;
      case 'b': ch = '\b'; ShiftCharN(1); break;
      case 'f': ch = '\f'; ShiftCharN(1); break;
      case 'n': ch = '\n'; ShiftCharN(1); break;
      case 'r': ch = '\r'; ShiftCharN(1); break;
      case 't': ch = '\t'; ShiftCharN(1); break;
      case 'v': ch = '\v'; ShiftCharN(1); break;
      default:
        goto lself;
      }
    }
  }
  else
  {
lself:
    if (strchr("\n\r", *p))
    {
lerr:
      //error("Unsupported or invalid character/string constant\n");
      errorChrStr();
    }
    ch = *p & 0xFFu;
#ifndef NO_WCHAR
    if (wide && ch > 0x7F && PrepDontSkipTokens)
      error("Only ASCII chars supported as wide chars\n");
#endif
    ShiftCharN(1);
  }
  return ch;
}

STATIC
void GetString(char terminator, int wide, int option)
{
  char* p = CharQueue;
  unsigned ch = '\0';
#ifndef NO_WCHAR
  unsigned chsz = wide ? SizeOfWideChar : 1;
#else
  unsigned chsz = 1;
#endif
  int i;

  TokenStringLen = 0;
  TokenStringSize = 0;
  TokenValueString[TokenStringLen] = '\0';

  ShiftCharN(1);
  while (!(*p == terminator || strchr("\n\r", *p)))
  {
    ch = GetCharValue(wide);
    switch (option)
    {
    case '#': // string literal (with file name) for #line and #include
      if (TokenStringLen == MAX_STRING_LEN)
        errorStrLen();
      TokenValueString[TokenStringLen++] = ch;
      TokenValueString[TokenStringLen] = '\0';
      TokenStringSize += chsz;
      break;
    case 'a': // string literal for asm()
      printf2("%c", ch);
      break;
    case 'd': // string literal / array of char in expression or initializer
      // Dump the char data to the appropriate data section
      for (i = 0; i < chsz; i++)
      {
        GenDumpChar(ch & 0xFFu);
        ch >>= 8;
        TokenStringLen++; // GenDumpChar() expects it to grow, doesn't know about wchar_t
      }
      TokenStringLen -= chsz;
      // fallthrough
    default: // skipped string literal (we may still need the size)
      if (TokenStringSize > UINT_MAX - chsz)
        errorStrLen();
      TokenStringSize += chsz;
      TokenStringLen++;
      break;
    } // endof switch (option)
  } // endof while (!(*p == '\0' || *p == terminator || strchr("\n\r", *p)))

  if (*p != terminator)
    //error("Unsupported or invalid character/string constant\n");
    errorChrStr();

  if (option == 'd')
    GenDumpChar(-1);

  ShiftCharN(1);

  SkipSpace(option != '#');
}

#ifndef NO_PREPROCESSOR
STATIC
void pushPrep(int NoSkip)
{
  if (PrepSp >= PREP_STACK_SIZE)
    error("Too many #if(n)def's\n");
  PrepStack[PrepSp][0] = PrepDontSkipTokens;
  PrepStack[PrepSp++][1] = NoSkip;
  PrepDontSkipTokens &= NoSkip;
}

STATIC
int popPrep(void)
{
  if (PrepSp <= 0)
    error("#else or #endif without #if(n)def\n");
  PrepDontSkipTokens = PrepStack[--PrepSp][0];
  return PrepStack[PrepSp][1];
}
#endif

#ifndef NO_FP
#include "fp.c"

#define FXNI2F    0
#define FXNU2F    1
#define FXNF2I    2
#define FXNF2U    3
#define FXNFADD   4
#define FXNFSUB   5
#define FXNFNEG   6
#define FXNFMUL   7
#define FXNFDIV   8
#define FXNFCMPL  9
#define FXNFCMPG 10
// Names of external functions for floating point arithmetic
char* FpFxnName[] =
{
  /*FXNI2F  */ "__floatsisf",
  /*FXNU2F  */ "__floatunsisf",
  /*FXNF2I  */ "__fixsfsi",
  /*FXNF2U  */ "__fixunssfsi",
  /*FXNFADD */ "__addsf3",
  /*FXNFSUB */ "__subsf3",
  /*FXNFNEG */ "__negsf2",
  /*FXNFMUL */ "__mulsf3",
  /*FXNFDIV */ "__divsf3",
  /*FXNFCMPL*/ "__lesf2",
  /*FXNFCMPG*/ "__gesf2"
};
#endif

STATIC
int GetNumber(void)
{
  char* p = CharQueue;
  int ch = *p;
  int leadingZero = (ch == '0');
  unsigned n = 0;
  int type = 0;
  int uSuffix = 0;
#ifdef CAN_COMPILE_32BIT
  int lSuffix = 0;
#endif
#ifndef NO_FP
  int mcnt = 0, eexp = 0;
#endif
  char* eTooBig = "Constant too big\n";

  // First, detect and handle hex constants. Octals can't be detected immediately
  // because floating-point constants also may begin with the digit 0.

  if (leadingZero && (p[1] == 'x' || p[1] == 'X'))
  {
    // this is a hex constant
    int cnt = 0;
    type = 'h';
    ShiftCharN(1);
    ShiftCharN(1);
    while ((ch = *p) != '\0' && (isdigit(ch & 0xFFu) || strchr("abcdefABCDEF", ch)))
    {
      if (ch >= 'a') ch -= 'a' - 10;
      else if (ch >= 'A') ch -= 'A' - 10;
      else ch -= '0';
      //if (PrepDontSkipTokens && (n * 16 / 16 != n || n * 16 + ch < n * 16))
      //  error(eTooBig);
      n = n * 16 + ch;
      ShiftCharN(1);
      cnt++;
    }
    if (!cnt)
      error("Invalid hexadecimal constant\n");
  }
#ifndef NO_FP
  else
  {
    // this is a decimal (possibly floating-point) or an octal constant, parse as decimal
    int mexp = 0, dot = 0;
    int ecnt = 0;
    type = 'd';
    // skip leading zeroes, if any
    while (*p == '0')
      ShiftCharN(1);
    // get digits of integral part, if any
    while (isdigit((ch = *p) & 0xFFu))
    {
      if (mcnt < MAX_CONST_DIGITS)
        ConstDigits[mcnt++] = ch - '0';
      else
        mexp++; // TBD??? overflow
      ShiftCharN(1);
    }
    // get dot and digits of fractional part, if any
    if (*p == '.')
    {
      dot = 1;
      ShiftCharN(1);
      // if the integral part is 0, skip leading zeroes in the fractional part, if any
      if (!mcnt)
        while (*p == '0')
          ShiftCharN(1), mexp--; // TBD??? overflow
      while (isdigit((ch = *p) & 0xFFu))
      {
        if (mcnt < MAX_CONST_DIGITS)
          ConstDigits[mcnt++] = ch - '0';
        mexp--; // TBD??? overflow
        ShiftCharN(1);
      }
    }
    // get exponent part, if any
    if (*p == 'e' || *p == 'E')
    {
      int esign = '+';
      ShiftCharN(1);
      if (*p == '+' || *p == '-')
        esign = *p, ShiftCharN(1);
      while (isdigit((ch = *p) & 0xFFu))
      {
        ch -= '0';
        if (//n * 10 / 10 != n ||
            n * 10 + ch < n * 10 ||
            n * 10 + ch > UINT_MAX >> 1)
        {
          if (PrepDontSkipTokens)
            error(eTooBig);
          n = 0;
        }
        n = n * 10 + ch;
        ShiftCharN(1);
        ecnt++;
      }
      if (!ecnt)
        error("Invalid float constant\n");
      eexp = n;
      if (esign == '-')
        eexp = -eexp;
    }
    if (dot || ecnt)
    {
      // this is a float constant (has either a dot or an exponent)
      // get float suffix, if any
      type = 'f';
      if (*p == 'f' || *p == 'F' || *p == 'l' || *p == 'L')
        ShiftCharN(1);
      // also drop trailing zeroes, if any
      while (mcnt)
      {
        if (ConstDigits[mcnt - 1])
          break;
        mexp++; // TBD??? overflow
        mcnt--;
      }
      if (!mcnt)
        ConstDigits[mcnt++] = 0, mexp = 0;
      if ((mexp >= 0 && eexp > INT_MAX - mexp) ||
          (mexp < 0 && eexp <= INT_MIN - (mexp + 1)))
      {
        if (PrepDontSkipTokens)
          error(eTooBig);
      }
      else
        eexp += mexp;
    }
    else
    {
      // handle decimal and octal integers
      int base = leadingZero ? 8 : 10;
      int i;
      type = leadingZero ? 'o' : 'd';
      for (i = 0; i < mcnt; i++)
      {
        ch = ConstDigits[i];
        if (ch >= base)
          error("Invalid octal constant\n");
        //if (PrepDontSkipTokens && (n * base / base != n || n * base + ch < n * base))
        //  error(eTooBig);
        n = n * base + ch;
      }
    }
  }
#else
  else
  {
    // handle decimal and octal integers
    int base = leadingZero ? 8 : 10;
    type = leadingZero ? 'o' : 'd';
    while ((ch = *p) >= '0' && ch < base + '0')
    {
      ch -= '0';
      if (PrepDontSkipTokens && (n * base + ch < n * base)) //n * base / base != n || 
        error(eTooBig);
      n = n * base + ch;
      ShiftCharN(1);
    }
  }
#endif

  // possible combinations of integer suffixes:
  //   none
  //   U
  //   UL
  //   L
  //   LU
#ifndef NO_FP
  if (type != 'f')
#endif
  {
    if ((ch = *p) == 'u' || ch == 'U')
    {
      uSuffix = 1;
      ShiftCharN(1);
    }
#ifdef CAN_COMPILE_32BIT
    if ((ch = *p) == 'l' || ch == 'L')
    {
      lSuffix = 1;
      ShiftCharN(1);
      if (!uSuffix && ((ch = *p) == 'u' || ch == 'U'))
      {
        uSuffix = 1;
        ShiftCharN(1);
      }
    }
#endif
  }

  if (!PrepDontSkipTokens)
  {
    // Don't fail on big constants when skipping tokens under #if
    TokenValueInt = 0;
    return tokNumInt;
  }

#ifndef NO_FP
  if (type == 'f')
  {
    TokenValueInt = d2f(ConstDigits, mcnt, eexp);
    return tokNumFloat;
  }
#endif

  // Ensure the constant fits into 16(32) bits
  if (
      (SizeOfWord == 2 && n >> 8 >> 8) // equiv. to SizeOfWord == 2 && n > 0xFFFF
#ifdef CAN_COMPILE_32BIT
      || (SizeOfWord == 2 && lSuffix) // long (which must have at least 32 bits) isn't supported in 16-bit models
      || (SizeOfWord == 4 && n >> 8 >> 12 >> 12) // equiv. to SizeOfWord == 4 && n > 0xFFFFFFFF
#endif
     )
    error("Constant too big for %d-bit type\n", SizeOfWord * 8);

  TokenValueInt = (int)n;

  // Unsuffixed (with 'u') integer constants (octal, decimal, hex)
  // fitting into 15(31) out of 16(32) bits are signed ints
  if (!uSuffix &&
      (
       (SizeOfWord == 2 && !(n >> 15)) // equiv. to SizeOfWord == 2 && n <= 0x7FFF
#ifdef CAN_COMPILE_32BIT
       || (SizeOfWord == 4 && !(n >> 8 >> 12 >> 11)) // equiv. to SizeOfWord == 4 && n <= 0x7FFFFFFF
#endif
      )
     )
    return tokNumInt;

  // Unlike octal and hex constants, decimal constants are always
  // a signed type. Error out when a decimal constant doesn't fit
  // into an int since currently there's no next bigger signed type
  // (e.g. long) to use instead of int.
  if (!uSuffix && type == 'd')
    error("Constant too big for %d-bit signed type\n", SizeOfWord * 8);

  return tokNumUint;
}

STATIC
int GetTokenInner(void)
{
  char* p = CharQueue;
  int ch = *p;
  int wide = 0;

  // these single-character tokens/operators need no further processing
  if (strchr(",;:()[]{}~?", ch))
  {
    ShiftCharN(1);
    return ch;
  }

  // parse multi-character tokens/operators

  // DONE: other assignment operators
  switch (ch)
  {
  case '+':
    if (p[1] == '+') { ShiftCharN(2); return tokInc; }
    if (p[1] == '=') { ShiftCharN(2); return tokAssignAdd; }
    ShiftCharN(1); return ch;
  case '-':
    if (p[1] == '-') { ShiftCharN(2); return tokDec; }
    if (p[1] == '=') { ShiftCharN(2); return tokAssignSub; }
    if (p[1] == '>') { ShiftCharN(2); return tokArrow; }
    ShiftCharN(1); return ch;
  case '!':
    if (p[1] == '=') { ShiftCharN(2); return tokNEQ; }
    ShiftCharN(1); return ch;
  case '=':
    if (p[1] == '=') { ShiftCharN(2); return tokEQ; }
    ShiftCharN(1); return ch;
  case '<':
    if (p[1] == '=') { ShiftCharN(2); return tokLEQ; }
    if (p[1] == '<') { ShiftCharN(2); if (p[0] != '=') return tokLShift; ShiftCharN(1); return tokAssignLSh; }
    ShiftCharN(1); return ch;
  case '>':
    if (p[1] == '=') { ShiftCharN(2); return tokGEQ; }
    if (p[1] == '>') { ShiftCharN(2); if (p[0] != '=') return tokRShift; ShiftCharN(1); return tokAssignRSh; }
    ShiftCharN(1); return ch;
  case '&':
    if (p[1] == '&') { ShiftCharN(2); return tokLogAnd; }
    if (p[1] == '=') { ShiftCharN(2); return tokAssignAnd; }
    ShiftCharN(1); return ch;
  case '|':
    if (p[1] == '|') { ShiftCharN(2); return tokLogOr; }
    if (p[1] == '=') { ShiftCharN(2); return tokAssignOr; }
    ShiftCharN(1); return ch;
  case '^':
    if (p[1] == '=') { ShiftCharN(2); return tokAssignXor; }
    ShiftCharN(1); return ch;
  case '.':
    if (p[1] == '.' && p[2] == '.') { ShiftCharN(3); return tokEllipsis; }
#ifndef NO_FP
    if (isdigit(p[1] & 0xFFu)) { return GetNumber(); }
#endif
    ShiftCharN(1); return ch;
  case '*':
    if (p[1] == '=') { ShiftCharN(2); return tokAssignMul; }
    ShiftCharN(1); return ch;
  case '%':
    if (p[1] == '=') { ShiftCharN(2); return tokAssignMod; }
    ShiftCharN(1); return ch;
  case '/':
    if (p[1] == '=') { ShiftCharN(2); return tokAssignDiv; }
    ShiftCharN(1); return ch;
  }

  // DONE: hex and octal constants
  if (isdigit(ch & 0xFFu))
    return GetNumber();

  // parse character and string constants
#ifndef NO_WCHAR
  if (ch == 'L' && (p[1] == '\'' || p[1] == '"'))
  {
    wide = 1; ShiftCharN(1); ch = *p;
  }
#endif
  if (ch == '\'')
  {
    unsigned v = 0;
    int cnt = 0;
#ifndef NO_WCHAR
    int max_cnt = wide ? 1 : SizeOfWord;
#else
    int max_cnt = SizeOfWord;
#endif
    ShiftCharN(1);
    if (strchr("'\n\r", *p))
      //error("Character constant too short\n");
      errorChrStr();
    do
    {
      v <<= 8;
      v |= GetCharValue(wide);
      if (++cnt > max_cnt)
        //error("Character constant too long\n");
        errorChrStr();
    } while (!strchr("'\n\r", *p));
    if (*p != '\'')
      //error("Unsupported or invalid character/string constant\n");
      errorChrStr();
    ShiftCharN(1);
#ifndef NO_WCHAR
    if (wide)
    {
      TokenValueInt = v;
#ifdef CAN_COMPILE_32BIT
      TokenValueInt -= (WideCharIsSigned && SizeOfWideChar == 2 &&
                        TokenValueInt >= 0x8000) * 0x10000;
#endif
      return tokNumCharWide;
    }
    else
#endif
    {
      if (cnt == 1)
      {
        TokenValueInt = v;
        TokenValueInt -= (CharIsSigned && TokenValueInt >= 0x80) * 0x100;
      }
      else
      {
        TokenValueInt = v;
#ifdef CAN_COMPILE_32BIT
        TokenValueInt -= (SizeOfWord == 2 && TokenValueInt >= 0x8000) * 0x10000;
#endif
      }
      return tokNumInt;
    }
  }
  else if (ch == '"')
  {
    // The caller of GetTokenInner()/GetToken() will call GetString('"', wide, 'd')
    // to complete string literal parsing and storing as appropriate
#ifndef NO_WCHAR
    return wide ? tokLitStrWide : tokLitStr;
#else
    return tokLitStr;
#endif
  }

  return tokEof;
}

#ifndef NO_PREPROCESSOR
STATIC
void Reserve4Expansion(char* name, int len)
{
  if (MAX_CHAR_QUEUE_LEN - CharQueueLen < len + 1)
    error("Too long expansion of macro '%s'\n", name);

  memmove(CharQueue + len + 1, CharQueue, CharQueueLen);

  CharQueue[len] = ' '; // space to avoid concatenation

  CharQueueLen += len + 1;
}
#endif

// TBD??? implement file I/O for input source code and output code (use fxn ptrs/wrappers to make librarization possible)
// DONE: support string literals
STATIC
int GetToken(void)
{
  char* p = CharQueue;
  int ch;
  int tok;

  for (;;)
  {
/* +-~* /% &|^! << >> && || < <= > >= == !=  () *[] ++ -- = += -= ~= *= /= %= &= |= ^= <<= >>= {} ,;: -> ... */

    // skip white space and comments
    SkipSpace(1);

    if ((ch = *p) == '\0')
    {
      // done with the current file, drop its record,
      // pick up the including files (if any) or terminate
      if (EndOfFiles())
        break;
      continue;
    }

    if ((tok = GetTokenInner()) != tokEof)
    {
      if (PrepDontSkipTokens)
        return tok;
      if (tok == tokLitStr)
        GetString('"', 0, 0);
#ifndef NO_WCHAR
      else if (tok == tokLitStrWide)
        GetString('"', 1, 0);
#endif
      continue;
    }

    // parse identifiers and reserved keywords
    if (ch == '_' || isalpha(ch & 0xFFu))
    {
#ifndef NO_PREPROCESSOR
      int midx;
#endif

      GetIdent();

      if (!PrepDontSkipTokens)
        continue;

      tok = GetTokenByWord(TokenIdentName);

#ifndef NO_PREPROCESSOR
      // TBD!!! think of expanding macros in the context of concatenating string literals,
      // maybe factor out this piece of code
      if (!strcmp(TokenIdentName, "__FILE__"))
      {
        char* p = FileNames[FileCnt - 1];
        int len = strlen(p);
        Reserve4Expansion(TokenIdentName, len + 2);
        *CharQueue = '"';
        memcpy(CharQueue + 1, p, len);
        CharQueue[len + 1] = '"';
        continue;
      }
      else if (!strcmp(TokenIdentName, "__LINE__"))
      {
        char s[(2 + CHAR_BIT * sizeof LineNo) / 3];
        char *p = lab2str(s + sizeof s, LineNo);
        int len = s + sizeof s - p;
        Reserve4Expansion(TokenIdentName, len);
        memcpy(CharQueue, p, len);
        continue;
      }
      else if ((midx = FindMacro(TokenIdentName)) >= 0)
      {
        // this is a macro identifier, need to expand it
        int len = MacroTable[midx];
        Reserve4Expansion(TokenIdentName, len);
        memcpy(CharQueue, MacroTable + midx + 1, len);
        continue;
      }
#endif

      // treat keywords auto, const, register, restrict and volatile as white space for now
      if ((tok == tokConst) | (tok == tokVolatile) |
          (tok == tokAuto) | (tok == tokRegister) |
          (tok == tokRestrict))
        continue;

      return tok;
    } // endof if (ch == '_' || isalpha(ch))

    // parse preprocessor directives
    if (ch == '#')
    {
      int line = 0;

      ShiftCharN(1);

      // Skip space
      SkipSpace(0);

      // Allow # not followed by a directive
      if (strchr("\r\n", *p))
        continue;

      // Get preprocessor directive
      if (isdigit(*p & 0xFFu))
      {
        // gcc-style #line directive without "line"
        line = 1;
      }
      else
      {
        GetIdent();
        if (!strcmp(TokenIdentName, "line"))
        {
          // C89-style #line directive
          SkipSpace(0);
          if (!isdigit(*p & 0xFFu))
            errorDirective();
          line = 1;
        }
      }

      if (line)
      {
        // Support for external, gcc-like, preprocessor output:
        //   # linenum filename flags
        //
        // no flags, flag = 1 -- start of a file
        //           flag = 2 -- return to a file after #include
        //        other flags -- uninteresting

        // DONE: should also support the following C89 form:
        // # line linenum filename-opt

        if (GetNumber() != tokNumInt)
          //error("Invalid line number in preprocessor output\n");
          errorDirective();
        line = TokenValueInt;

        SkipSpace(0);

        if (*p == '"' || *p == '<')
        {
          if (*p == '"')
            GetString('"', 0, '#');
          else
            GetString('>', 0, '#');

          if (strlen(TokenValueString) > MAX_FILE_NAME_LEN)
            //error("File name too long in preprocessor output\n");
            errorFileName();
          strcpy(FileNames[FileCnt - 1], TokenValueString);
        }

        // Ignore gcc-style #line's flags, if any
        while (!strchr("\r\n", *p))
          ShiftCharN(1);

        LineNo = line - 1; // "line" is the number of the next line
        LinePos = 1;

        continue;
      } // endof if (line)

#ifndef NO_PPACK
      if (!strcmp(TokenIdentName, "pragma"))
      {
        int canHaveNumber = 1, hadNumber = 0;

        if (!PrepDontSkipTokens)
        {
          while (!strchr("\r\n", *p))
            ShiftCharN(1);
          continue;
        }

        SkipSpace(0);
        GetIdent();
        if (strcmp(TokenIdentName, "pack"))
          errorDirective();
        // TBD??? fail if inside a structure declaration
        SkipSpace(0);
        if (*p == '(')
          ShiftCharN(1);
        SkipSpace(0);

        if (*p == 'p')
        {
          GetIdent();
          if (!strcmp(TokenIdentName, "push"))
          {
            SkipSpace(0);
            if (*p == ',')
            {
              ShiftCharN(1);
              SkipSpace(0);
              if (!isdigit(*p & 0xFFu) || GetNumber() != tokNumInt)
                errorDirective();
              hadNumber = 1;
            }
            if (PragmaPackSp >= PPACK_STACK_SIZE)
              error("#pragma pack stack overflow\n");
            PragmaPackValues[PragmaPackSp++] = PragmaPackValue;
          }
          else if (!strcmp(TokenIdentName, "pop"))
          {
            if (PragmaPackSp <= 0)
              error("#pragma pack stack underflow\n");
            PragmaPackValue = PragmaPackValues[--PragmaPackSp];
          }
          else
            errorDirective();
          SkipSpace(0);
          canHaveNumber = 0;
        }

        if (canHaveNumber && isdigit(*p & 0xFFu))
        {
          if (GetNumber() != tokNumInt)
            errorDirective();
          hadNumber = 1;
          SkipSpace(0);
        }

        if (hadNumber)
        {
          PragmaPackValue = TokenValueInt;
          if (PragmaPackValue <= 0 ||
              PragmaPackValue > SizeOfWord ||
              PragmaPackValue & (PragmaPackValue - 1))
            error("Invalid alignment value\n");
        }
        else if (canHaveNumber)
        {
          PragmaPackValue = SizeOfWord;
        }

        if (*p != ')')
          errorDirective();
        ShiftCharN(1);

        SkipSpace(0);
        if (!strchr("\r\n", *p))
          errorDirective();
        continue;
      }
#endif

#ifndef NO_PREPROCESSOR
      if (!strcmp(TokenIdentName, "define"))
      {
        // Skip space and get macro name
        SkipSpace(0);
        GetIdent();

        if (!PrepDontSkipTokens)
        {
          SkipSpace(0);
          while (!strchr("\r\n", *p))
            ShiftCharN(1);
          continue;
        }

        if (FindMacro(TokenIdentName) >= 0)
          error("Redefinition of macro '%s'\n", TokenIdentName);
        if (*p == '(')
          //error("Unsupported type of macro '%s'\n", TokenIdentName);
          errorDirective();

        AddMacroIdent(TokenIdentName);

        SkipSpace(0);

        // accumulate the macro expansion text
        while (!strchr("\r\n", *p))
        {
          AddMacroExpansionChar(*p);
          ShiftCharN(1);
          if (*p != '\0' && (strchr(" \t", *p) || (*p == '/' && (p[1] == '/' || p[1] == '*'))))
          {
            SkipSpace(0);
            AddMacroExpansionChar(' ');
          }
        }
        AddMacroExpansionChar('\0');

        continue;
      }
      else if (!strcmp(TokenIdentName, "undef"))
      {
        // Skip space and get macro name
        SkipSpace(0);
        GetIdent();

        if (PrepDontSkipTokens)
          UndefineMacro(TokenIdentName);

        SkipSpace(0);
        if (!strchr("\r\n", *p))
          //error("Invalid preprocessor directive\n");
          errorDirective();
        continue;
      }
      else if (!strcmp(TokenIdentName, "include"))
      {
        int quot;

        // Skip space and get file name
        SkipSpace(0);

        quot = *p;
        if (*p == '"')
          GetString('"', 0, '#');
        else if (*p == '<')
          GetString('>', 0, '#');
        else
          //error("Invalid file name\n");
          errorFileName();

        SkipSpace(0);
        if (!strchr("\r\n", *p))
          //error("Unsupported or invalid preprocessor directive\n");
          errorDirective();

        if (PrepDontSkipTokens)
          IncludeFile(quot);

        continue;
      }
      else if (!strcmp(TokenIdentName, "ifdef"))
      {
        int def;
        // Skip space and get macro name
        SkipSpace(0);
        GetIdent();
        def = FindMacro(TokenIdentName) >= 0;
        SkipSpace(0);
        if (!strchr("\r\n", *p))
          //error("Invalid preprocessor directive\n");
          errorDirective();
        pushPrep(def);
        continue;
      }
      else if (!strcmp(TokenIdentName, "ifndef"))
      {
        int def;
        // Skip space and get macro name
        SkipSpace(0);
        GetIdent();
        def = FindMacro(TokenIdentName) >= 0;
        SkipSpace(0);
        if (!strchr("\r\n", *p))
          //error("Invalid preprocessor directive\n");
          errorDirective();
        pushPrep(!def);
        continue;
      }
      else if (!strcmp(TokenIdentName, "else"))
      {
        int def;
        SkipSpace(0);
        if (!strchr("\r\n", *p))
          //error("Invalid preprocessor directive\n");
          errorDirective();
        def = popPrep();
        if (def >= 2)
          error("#else or #endif without #if(n)def\n");
        pushPrep(2 + !def); // #else works in opposite way to its preceding #if(n)def
        continue;
      }
      else if (!strcmp(TokenIdentName, "endif"))
      {
        SkipSpace(0);
        if (!strchr("\r\n", *p))
          //error("Invalid preprocessor directive\n");
          errorDirective();
        popPrep();
        continue;
      }

      if (!PrepDontSkipTokens)
      {
        // If skipping code and directives under #ifdef/#ifndef/#else,
        // ignore unsupported directives #if, #elif, #error (no error checking)
        if (!strcmp(TokenIdentName, "if"))
          pushPrep(0);
        else if (!strcmp(TokenIdentName, "elif"))
          popPrep(), pushPrep(0);
        SkipLine();
        continue;
      }
#endif // #ifndef NO_PREPROCESSOR

      //error("Unsupported or invalid preprocessor directive\n");
      errorDirective();
    } // endof if (ch == '#')

    error("Invalid or unsupported character with code 0x%02X\n", *p & 0xFFu);
  } // endof for (;;)

  return tokEof;
}

STATIC
void errorRedecl(char* s)
{
  error("Invalid or unsupported redeclaration of '%s'\n", s);
}

#ifndef CAN_COMPILE_32BIT
#error target requires a 32-bit compiler
#endif

#include "backend.c"

// expr.c code

STATIC
void push2(int v, int v2)
{
  if (sp >= STACK_SIZE)
    //error("expression stack overflow!\n");
    errorLongExpr();
  stack[sp][0] = v;
  stack[sp++][1] = v2;
}

STATIC
void push(int v)
{
  push2(v, 0);
}

STATIC
int stacktop()
{
  if (sp == 0)
    //error("expression stack underflow!\n");
    errorInternal(3);
  return stack[sp - 1][0];
}

STATIC
int pop2(int* v2)
{
  int v = stacktop();
  *v2 = stack[sp - 1][1];
  sp--;
  return v;
}

int pop()
{
  int v2;
  return pop2(&v2);
}

STATIC
void ins2(int pos, int v, int v2)
{
  if (sp >= STACK_SIZE)
    //error("expression stack overflow!\n");
    errorLongExpr();
  memmove(&stack[pos + 1], &stack[pos], sizeof(stack[0]) * (sp - pos));
  stack[pos][0] = v;
  stack[pos][1] = v2;
  sp++;
}

STATIC
void ins(int pos, int v)
{
  ins2(pos, v, 0);
}

STATIC
void del(int pos, int cnt)
{
  memmove(stack[pos],
          stack[pos + cnt],
          sizeof(stack[0]) * (sp - (pos + cnt)));
  sp -= cnt;
}

#ifndef NO_FP
STATIC
void rev(int pos, int cnt)
{
  // reverse cnt items at pos on the stack
  int (*p1)[2] = stack + pos, (*p2)[2] = p1 + cnt - 1;
  while (p1 < p2)
  {
    int t0 = **p1;
    int t1 = (*p1)[1];
    **p1 = **p2;
    (*p1++)[1] = (*p2)[1];
    **p2 = t0;
    (*p2--)[1] = t1;
  }
}

STATIC
void swap(int pos, int cntlo, int cnthi)
{
  // swap cntlo items at pos with cnthi items at pos + cntlo
  rev(pos, cntlo);
  rev(pos + cntlo, cnthi);
  rev(pos, cntlo + cnthi);
}
#endif

STATIC
void pushop2(int v, int v2)
{
  if (opsp >= OPERATOR_STACK_SIZE)
    //error("operator stack overflow!\n");
    errorLongExpr();
  opstack[opsp][0] = v;
  opstack[opsp++][1] = v2;
}

STATIC
void pushop(int v)
{
  pushop2(v, 0);
}

STATIC
int opstacktop()
{
  if (opsp == 0)
    //error("operator stack underflow!\n");
    errorInternal(4);
  return opstack[opsp - 1][0];
}

STATIC
int popop2(int* v2)
{
  int v = opstacktop();
  *v2 = opstack[opsp - 1][1];
  opsp--;
  return v;
}

STATIC
int popop()
{
  int v2;
  return popop2(&v2);
}

STATIC
int isop(int tok)
{
  static unsigned char toks[] =
  {
    '!',
    '~',
    '&',
    '*',
    '/', '%',
    '+', '-',
    '|', '^',
    '<', '>',
    '=',
    tokLogOr, tokLogAnd,
    tokEQ, tokNEQ,
    tokLEQ, tokGEQ,
    tokLShift, tokRShift,
    tokInc, tokDec,
    tokSizeof,
    tokAssignMul, tokAssignDiv, tokAssignMod,
    tokAssignAdd, tokAssignSub,
    tokAssignLSh, tokAssignRSh,
    tokAssignAnd, tokAssignXor, tokAssignOr,
    tokComma,
    '?'
  };
  unsigned i;
  for (i = 0; i < division(sizeof toks , sizeof toks[0]); i++)
    if (toks[i] == tok)
      return 1;
  return 0;
}

STATIC
int isunary(int tok)
{
  return (tok == '!') | (tok == '~') | (tok == tokInc) | (tok == tokDec) | (tok == tokSizeof);
}

STATIC
int preced(int tok)
{
  switch (tok)
  {
  case '*': case '/': case '%': return 13;
  case '+': case '-': return 12;
  case tokLShift: case tokRShift: return 11;
  case '<': case '>': case tokLEQ: case tokGEQ: return 10;
  case tokEQ: case tokNEQ: return 9;
  case '&': return 8;
  case '^': return 7;
  case '|': return 6;
  case tokLogAnd: return 5;
  case tokLogOr: return 4;
  case '?': case ':': return 3;
  case '=':
  case tokAssignMul: case tokAssignDiv: case tokAssignMod:
  case tokAssignAdd: case tokAssignSub:
  case tokAssignLSh: case tokAssignRSh:
  case tokAssignAnd: case tokAssignXor: case tokAssignOr:
    return 2;
  case tokComma:
    return 1;
  }
  return 0;
}

STATIC
int precedGEQ(int lfttok, int rhttok)
{
  // DONE: rethink the comma operator as it could be implemented similarly
  // DONE: is this correct:???
  int pl = preced(lfttok);
  int pr = preced(rhttok);
  // ternary/conditional operator ?: is right-associative
  if (pl == 3 && pr >= 3)
    pl = 0;
  // assignment is right-associative
  if (pl == 2 && pr >= 2)
    pl = 0;
  return pl >= pr;
}

STATIC
int expr(int tok, int* gotUnary, int commaSeparator);

STATIC
char* lab2str(char* p, int n)
{
  do
  {
    *--p = '0' + modulo(n , 10);
    n = division(n, 10);
  } while (n);

  return p;
}

STATIC
int exprUnary(int tok, int* gotUnary, int commaSeparator, int argOfSizeOf)
{
  static int sizeofLevel = 0;

  int decl = 0;
  *gotUnary = 0;

  if (isop(tok) && (isunary(tok) || strchr("&*+-", tok)))
  {
    int lastTok = tok;
    int sizeofLevelInc = lastTok == tokSizeof;

    sizeofLevel += sizeofLevelInc;
    tok = exprUnary(GetToken(), gotUnary, commaSeparator, sizeofLevelInc);
    sizeofLevel -= sizeofLevelInc;

    if (!*gotUnary)
      //error("exprUnary(): primary expression expected after token %s\n", GetTokenName(lastTok));
      errorUnexpectedToken(tok);
    switch (lastTok)
    {
    // DONE: remove all collapsing of all unary operators.
    // It's wrong because type checking must occur before any optimizations.
    // WRONG: DONE: collapse alternating & and * (e.g. "*&*&x" "&*&*x")
    // WRONGISH: DONE: replace prefix ++/-- with +=1/-=1
    case '&':
      push(tokUnaryAnd);
      break;
    case '*':
      push(tokUnaryStar);
      break;
    case '+':
      push(tokUnaryPlus);
      break;
    case '-':
      push(tokUnaryMinus);
      break;
    case '!':
      // replace "!" with "== 0"
      push(tokNumInt);
      push(tokEQ);
      break;
    default:
      push(lastTok);
      break;
    }
  }
  else
  {
    int inspos = sp;

    if (tok == tokNumInt ||
#ifndef NO_FP
        tok == tokNumFloat ||
#endif
#ifndef NO_WCHAR
        tok == tokNumCharWide ||
#endif
        tok == tokNumUint)
    {
      push2(tok, TokenValueInt);
      *gotUnary = 1;
      tok = GetToken();
    }
    else if (tok == tokLitStr
#ifndef NO_WCHAR
             || tok == tokLitStrWide
#endif
            )
    {
      int lbl = LabelCnt++;
      int id;
      int ltok = tok;
#ifndef NO_WCHAR
      int wide = tok == tokLitStrWide;
      unsigned chsz = wide ? SizeOfWideChar : 1;
#else
      int wide = 0;
      unsigned chsz = 1;
#endif
      unsigned sz = chsz;

      // imitate definition: char #[len] = "...";

      if (!sizeofLevel)
      {
        if (CurHeaderFooter)
          puts2(CurHeaderFooter[1]);
        puts2(RoDataHeaderFooter[0]);

#ifndef NO_WCHAR
        if (wide)
          GenWordAlignment(0);
#endif
        GenNumLabel(lbl);
      }

      do
      {
        GetString('"', wide, sizeofLevel ? 0 : 'd'); // throw away string data inside sizeof, e.g. sizeof "a" or sizeof("a" + 1)
        if (sz + TokenStringSize < sz ||
            sz + TokenStringSize >= truncUint(-1))
          errorStrLen();
        sz += TokenStringSize;
        tok = GetToken();
      } while (tok == ltok); // concatenate adjacent string literals

#ifndef NO_WCHAR
      if ((ltok ^ (tokLitStr ^ tokLitStrWide)) == tok)
        errorWideNonWide();
#endif

      if (!sizeofLevel)
      {
        GenZeroData(chsz, 0);

        puts2(RoDataHeaderFooter[1]);
        if (CurHeaderFooter)
          puts2(CurHeaderFooter[0]);
      }

      // DONE: can this break incomplete yet declarations???, e.g.: int x[sizeof("az")][5];
      PushSyntax2(tokIdent, id = AddNumericIdent(lbl));
      PushSyntax('[');
      PushSyntax2(tokNumUint, division(sz, chsz));
      PushSyntax(']');
#ifndef NO_WCHAR
      PushSyntax(wide ? WideCharType1 : tokChar);
#else
      PushSyntax(tokChar);
#endif

      push2(tokIdent, id);
      *gotUnary = 1;
    }
    else if (tok == tokIdent)
    {
      push2(tok, AddIdent(TokenIdentName));
      *gotUnary = 1;
      tok = GetToken();
    }
    else if (tok == '(')
    {
      tok = GetToken();
      decl = TokenStartsDeclaration(tok, 1);

      if (decl)
      {
        int synPtr;
        int lbl = LabelCnt++;
        char s[1 + (2 + CHAR_BIT * sizeof lbl) / 3 + sizeof "<something>" - 1];
        char *p = s + sizeof s;

        tok = ParseDecl(tok, NULL, !argOfSizeOf, 0);
        if (tok != ')')
          //error("exprUnary(): ')' expected, unexpected token %s\n", GetTokenName(tok));
          errorUnexpectedToken(tok);
        synPtr = FindSymbol("<something>");

        // Rename "<something>" to "<something#>", where # is lbl.
        // This makes the nameless declaration uniquely identifiable by name.

        *--p = '\0';
        *--p = ")>"[argOfSizeOf]; // differentiate casts (something#) from not casts <something#>

        p = lab2str(p, lbl);

        p -= sizeof "<something>" - 2 - 1;
        memcpy(p, "something", sizeof "something" - 1);

        *--p = "(<"[argOfSizeOf]; // differentiate casts (something#) from not casts <something#>

        SyntaxStack1[synPtr] = AddIdent(p);
        tok = GetToken();
        if (argOfSizeOf)
        {
          // expression: sizeof(type)
          *gotUnary = 1;
        }
        else
        {
          // unary type cast operator: (type)
          decl = 0;
          tok = exprUnary(tok, gotUnary, commaSeparator, 0);
          if (!*gotUnary)
            //error("exprUnary(): primary expression expected after '(type)'\n");
            errorUnexpectedToken(tok);
        }
        push2(tokIdent, SyntaxStack1[synPtr]);
      }
      else
      {
        tok = expr(tok, gotUnary, 0);
        if (tok != ')')
          //error("exprUnary(): ')' expected, unexpected token %s\n", GetTokenName(tok));
          errorUnexpectedToken(tok);
        if (!*gotUnary)
          //error("exprUnary(): primary expression expected in '()'\n");
          errorUnexpectedToken(tok);
        tok = GetToken();
      }
    }

    while (*gotUnary && !decl)
    {
      // DONE: f(args1)(args2) and the like: need stack order: args2, args1, f, (), ()
      // DONE: reverse the order of evaluation of groups of args in
      //       f(args1)(args2)(args3)
      // DONE: reverse the order of function argument evaluation for variadic functions
      //       we want 1st arg to be the closest to the stack top.
      // DONE: (args)[index] can be repeated interchangeably indefinitely
      // DONE: (expr)() & (expr)[]
      // DONE: [index] can be followed by ++/--, which can be followed by [index] and so on...
      // DONE: postfix ++/-- & differentiate from prefix ++/--

      if (tok == '(')
      {
        int acnt = 0;
        ins(inspos, '(');
        for (;;)
        {
          int pos2 = sp;

          tok = GetToken();
          tok = expr(tok, gotUnary, 1);

          // Reverse the order of argument evaluation, which is important for
          // variadic functions like printf():
          // we want 1st arg to be the closest to the stack top.
          // This also reverses the order of evaluation of all groups of
          // arguments.
          while (pos2 < sp)
          {
            // TBD??? not quite efficient
            int v, v2;
            v = pop2(&v2);
            ins2(inspos + 1, v, v2);
            pos2++;
          }

          if (tok == ',')
          {
            if (!*gotUnary)
              //error("exprUnary(): primary expression (fxn argument) expected before ','\n");
              errorUnexpectedToken(tok);
            acnt++;
            ins(inspos + 1, ','); // helper argument separator (hint for expression evaluator)
            continue; // off to next arg
          }
          if (tok == ')')
          {
            if (acnt && !*gotUnary)
              //error("exprUnary(): primary expression (fxn argument) expected between ',' and ')'\n");
              errorUnexpectedToken(tok);
            *gotUnary = 1; // don't fail for 0 args in ()
            break; // end of args
          }
          // DONE: think of inserting special arg pseudo tokens for verification purposes
          //error("exprUnary(): ',' or ')' expected, unexpected token %s\n", GetTokenName(tok));
          errorUnexpectedToken(tok);
        } // endof for(;;) for fxn args
        push(')');
      }
      else if (tok == '[')
      {
        tok = GetToken();
        tok = expr(tok, gotUnary, 0);
        if (!*gotUnary)
          //error("exprUnary(): primary expression expected in '[]'\n");
          errorUnexpectedToken(tok);
        if (tok != ']')
          //error("exprUnary(): ']' expected, unexpected token %s\n", GetTokenName(tok));
          errorUnexpectedToken(tok);
        // TBD??? add implicit casts to size_t of array indicies.
        // E1[E2] -> *(E1 + E2)
        // push('[');
        push('+');
        push(tokUnaryStar);
      }
      // WRONG: DONE: replace postfix ++/-- with (+=1)-1/(-=1)+1
      else if (tok == tokInc)
      {
        push(tokPostInc);
      }
      else if (tok == tokDec)
      {
        push(tokPostDec);
      }
      else if (tok == '.' || tok == tokArrow)
      {
        // transform a.b into (&a)->b
        if (tok == '.')
          push(tokUnaryAnd);
        tok = GetToken();
        if (tok != tokIdent)
          errorUnexpectedToken(tok);
        push2(tok, AddIdent(TokenIdentName));
        // "->" in "a->b" will function as "+" in "*(type_of_b*)((char*)a + offset_of_b_in_a)"
        push(tokArrow);
        push(tokUnaryStar);
      }
      else
      {
        break;
      }
      tok = GetToken();
    } // endof while (*gotUnary)
  }

  if (tok == ',' && !commaSeparator)
    tok = tokComma;

  return tok;
}

STATIC
int expr(int tok, int* gotUnary, int commaSeparator)
{
  *gotUnary = 0;
  pushop(tokEof);

  tok = exprUnary(tok, gotUnary, commaSeparator, 0);

  while (tok != tokEof && strchr(",;:)]}", tok) == NULL && *gotUnary)
  {
    if (isop(tok) && !isunary(tok))
    {
      while (precedGEQ(opstacktop(), tok))
      {
        int v, v2;
        v = popop2(&v2);
        // move ?expr: as a whole to the expression stack as "expr?"
        if (v == '?')
        {
          int cnt = v2;
          while (cnt--)
          {
            v = popop2(&v2);
            push2(v, v2);
          }
          v = '?';
          v2 = 0;
        }
        push2(v, v2);
      }

      // here: preced(postacktop()) < preced(tok)

      // treat the ternary/conditional operator ?expr: as a pseudo binary operator
      if (tok == '?')
      {
        int ssp = sp;
        int cnt;

        tok = expr(GetToken(), gotUnary, 0);
        if (!*gotUnary || tok != ':')
          errorUnexpectedToken(tok);

        // move ?expr: as a whole to the operator stack
        // this is beautiful and ugly at the same time
        cnt = sp - ssp;
        while (sp > ssp)
        {
          int v, v2;
          v = pop2(&v2);
          pushop2(v, v2);
        }

        // remember the length of the expression between ? and :
        pushop2('?', cnt);
      }
      else
      {
        pushop(tok);
      }

      tok = exprUnary(GetToken(), gotUnary, commaSeparator, 0);
      // DONE: figure out a check to see if exprUnary() fails to add a rhs operand
      if (!*gotUnary)
        //error("expr(): primary expression expected after token %s\n", GetTokenName(lastTok));
        errorUnexpectedToken(tok);

      continue;
    }

    //error("expr(): Unexpected token %s\n", GetTokenName(tok));
    errorUnexpectedToken(tok);
  }

  while (opstacktop() != tokEof)
  {
    int v, v2;
    v = popop2(&v2);
    // move ?expr: as a whole to the expression stack as "expr?"
    if (v == '?')
    {
      int cnt = v2;
      while (cnt--)
      {
        v = popop2(&v2);
        push2(v, v2);
      }
      v = '?';
      v2 = 0;
    }
    push2(v, v2);
  }

  popop();
  return tok;
}

STATIC
int isAnyPtr(int ExprTypeSynPtr)
{
  if (ExprTypeSynPtr < 0)
    return 1;
  switch (SyntaxStack0[ExprTypeSynPtr])
  {
  case '*':
  case '[':
  case '(':
    return 1;
  }
  return 0;
}

STATIC
int derefAnyPtr(int ExprTypeSynPtr)
{
  if (ExprTypeSynPtr < 0)
    return -ExprTypeSynPtr;
  switch (SyntaxStack0[ExprTypeSynPtr])
  {
  case '*':
    return ExprTypeSynPtr + 1;
  case '[':
    return ExprTypeSynPtr + 3;
  case '(':
    return ExprTypeSynPtr;
  }
  errorInternal(22);
  return -1;
}

STATIC
void decayArray(int* ExprTypeSynPtr, int arithmetic)
{
  // Dacay arrays to pointers to their first elements
  if (*ExprTypeSynPtr >= 0 && SyntaxStack0[*ExprTypeSynPtr] == '[')
  {
    (*ExprTypeSynPtr) += 3;
    // we cannot insert another '*' into the type to make it a pointer
    // to the first element, so make the index into the type negative
    *ExprTypeSynPtr = -*ExprTypeSynPtr;
  }

  // DONE: disallow arithmetic on pointers to void
  // DONE: disallow function pointers
  if (arithmetic && isAnyPtr(*ExprTypeSynPtr))
  {
    int pointee = derefAnyPtr(*ExprTypeSynPtr);
    switch (SyntaxStack0[pointee])
    {
    case tokVoid:
      //error("decayArray(): cannot do pointer arithmetic on a pointer to 'void'\n");
      errorUnexpectedVoid();
    default:
      //error("decayArray(): cannot do pointer arithmetic on a pointer to an incomplete type\n");
      if (!GetDeclSize(pointee, 0))
      // "fallthrough"
    case '(':
        //error("decayArray(): cannot do pointer arithmetic on a pointer to a function\n");
        errorOpType();
    }
  }
}

STATIC
void lvalueCheck(int ExprTypeSynPtr, int pos)
{
  if (ExprTypeSynPtr >= 0 &&
      (SyntaxStack0[ExprTypeSynPtr] == '[' || SyntaxStack0[ExprTypeSynPtr] == '('))
  {
    // we can have arrays formed by dereference, e.g.
    //   char (*pac)[1]; // *pac is array of 1 char
    //                   // ++*pac or (*pac)-- are not allowed
    // and likewise functions, e.g.
    //   int (*pf)(int); // *pf is a function taking int and returning int
    //                   // *pf = 0; is not allowed
    // and that dereference shouldn't be confused for lvalue,
    // hence explicitly checking for array and function types
    //error("exprval(): lvalue expected\n");
    errorNotLvalue();
  }
  // lvalue is a dereferenced address, check for a dereference
  if (stack[pos][0] != tokUnaryStar)
    //error("exprval(): lvalue expected\n");
    errorNotLvalue();
}

STATIC
void nonVoidTypeCheck(int ExprTypeSynPtr)
{
  if (ExprTypeSynPtr >= 0 && SyntaxStack0[ExprTypeSynPtr] == tokVoid)
    //error("nonVoidTypeCheck(): unexpected operand type 'void' for operator '%s'\n", GetTokenName(tok));
    errorUnexpectedVoid();
}

STATIC
void scalarTypeCheck(int ExprTypeSynPtr)
{
  nonVoidTypeCheck(ExprTypeSynPtr);

  if (ExprTypeSynPtr >= 0 && SyntaxStack0[ExprTypeSynPtr] == tokStructPtr)
    errorOpType();
}

STATIC
void numericTypeCheck(int ExprTypeSynPtr)
{
  if (ExprTypeSynPtr >= 0)
    switch (SyntaxStack0[ExprTypeSynPtr])
    {
    case tokChar:
    case tokSChar:
    case tokUChar:
#ifdef CAN_COMPILE_32BIT
    case tokShort:
    case tokUShort:
#endif
    case tokInt:
    case tokUnsigned:
#ifndef NO_FP
    case tokFloat:
#endif
      return;
    }
  //error("numericTypeCheck(): unexpected operand type for operator '%s', numeric type expected\n", GetTokenName(tok));
  errorOpType();
}

#ifndef NO_FP
STATIC
void nonFloatTypeCheck(int ExprTypeSynPtr)
{
  if (ExprTypeSynPtr >= 0 && SyntaxStack0[ExprTypeSynPtr] == tokFloat)
    errorOpType();
}
#endif

STATIC
void anyIntTypeCheck(int ExprTypeSynPtr)
{
  // Check for any integer type
  numericTypeCheck(ExprTypeSynPtr);
#ifndef NO_FP
  nonFloatTypeCheck(ExprTypeSynPtr);
#endif
}

#ifndef NO_FP
STATIC
int isFloat(int ExprTypeSynPtr)
{
  return ExprTypeSynPtr >= 0 && SyntaxStack0[ExprTypeSynPtr] == tokFloat;
}
#endif

STATIC
int isUint(int ExprTypeSynPtr)
{
  return ExprTypeSynPtr >= 0 && SyntaxStack0[ExprTypeSynPtr] == tokUnsigned;
}

STATIC
void compatCheck(int* ExprTypeSynPtr, int TheOtherExprTypeSynPtr, int ConstExpr[2], int lidx, int ridx)
{
  int exprTypeSynPtr = *ExprTypeSynPtr;
  int c = 0;
  int lptr, rptr, lnum, rnum;

  // (un)decay/convert functions to pointers to functions
  // and to simplify matters convert all '*' pointers to negative type indices
  if (exprTypeSynPtr >= 0)
  {
    switch (SyntaxStack0[exprTypeSynPtr])
    {
    case '*':
      exprTypeSynPtr++;
      // fallthrough
    case '(':
      exprTypeSynPtr = -exprTypeSynPtr;
    }
    *ExprTypeSynPtr = exprTypeSynPtr;
  }
  if (TheOtherExprTypeSynPtr >= 0)
  {
    switch (SyntaxStack0[TheOtherExprTypeSynPtr])
    {
    case '*':
      TheOtherExprTypeSynPtr++;
      // fallthrough
    case '(':
      TheOtherExprTypeSynPtr = -TheOtherExprTypeSynPtr;
    }
  }
  lptr = exprTypeSynPtr < 0;
  rptr = TheOtherExprTypeSynPtr < 0;
  lnum = !lptr && (SyntaxStack0[exprTypeSynPtr] == tokInt ||
#ifndef NO_FP
                   SyntaxStack0[exprTypeSynPtr] == tokFloat ||
#endif
                   SyntaxStack0[exprTypeSynPtr] == tokUnsigned);
  rnum = !rptr && (SyntaxStack0[TheOtherExprTypeSynPtr] == tokInt ||
#ifndef NO_FP
                   SyntaxStack0[TheOtherExprTypeSynPtr] == tokFloat ||
#endif
                   SyntaxStack0[TheOtherExprTypeSynPtr] == tokUnsigned);

  // both operands have arithmetic type
  // (arithmetic operands have been already promoted):
  if (lnum && rnum)
    return;

  // both operands have void type:
  if (!lptr && SyntaxStack0[exprTypeSynPtr] == tokVoid &&
      !rptr && SyntaxStack0[TheOtherExprTypeSynPtr] == tokVoid)
    return;

  // one operand is a pointer and the other is NULL constant
  // ((void*)0 is also a valid null pointer constant),
  // the type of the expression is that of the pointer:
  if (lptr &&
      ((rnum && ConstExpr[1] && truncInt(stack[ridx][1]) == 0) ||
       (rptr && SyntaxStack0[-TheOtherExprTypeSynPtr] == tokVoid &&
        (stack[ridx][0] == tokNumInt || stack[ridx][0] == tokNumUint) &&
        truncInt(stack[ridx][1]) == 0)))
    return;
  if (rptr &&
      ((lnum && ConstExpr[0] && truncInt(stack[lidx][1]) == 0) ||
       (lptr && SyntaxStack0[-exprTypeSynPtr] == tokVoid &&
        (stack[lidx][0] == tokNumInt || stack[lidx][0] == tokNumUint) &&
        truncInt(stack[lidx][1]) == 0)))
  {
    *ExprTypeSynPtr = TheOtherExprTypeSynPtr;
    return;
  }

  // not expecting non-pointers beyond this point
  if (!(lptr && rptr))
    errorOpType();

  // one operand is a pointer and the other is a pointer to void
  // (except (void*)0 (AKA NULL), which is different from other pointers to void),
  // the type of the expression is pointer to void:
  if (SyntaxStack0[-exprTypeSynPtr] == tokVoid)
    return;
  if (SyntaxStack0[-TheOtherExprTypeSynPtr] == tokVoid)
  {
    *ExprTypeSynPtr = TheOtherExprTypeSynPtr;
    return;
  }

  // both operands are pointers to compatible types:

  if (exprTypeSynPtr == TheOtherExprTypeSynPtr)
    return;

  exprTypeSynPtr = -exprTypeSynPtr;
  TheOtherExprTypeSynPtr = -TheOtherExprTypeSynPtr;

  for (;;)
  {
    int tok = SyntaxStack0[exprTypeSynPtr];
    if (tok != SyntaxStack0[TheOtherExprTypeSynPtr])
      errorOpType();

    if (tok != tokIdent &&
        SyntaxStack1[exprTypeSynPtr] != SyntaxStack1[TheOtherExprTypeSynPtr])
      errorOpType();

    c += (tok == '(') - (tok == ')') + (tok == '[') - (tok == ']');

    if (!c)
    {
      switch (tok)
      {
      case tokVoid:
      case tokChar: case tokSChar: case tokUChar:
#ifdef CAN_COMPILE_32BIT
      case tokShort: case tokUShort:
#endif
      case tokInt: case tokUnsigned:
#ifndef NO_FP
      case tokFloat:
#endif
      case tokStructPtr:
        return;
      }
    }

    exprTypeSynPtr++;
    TheOtherExprTypeSynPtr++;
  }
}

STATIC
void shiftCountCheck(int *psr, int idx, int ExprTypeSynPtr)
{
  int sr = *psr;
  // can't shift by a negative count and by a count exceeding
  // the number of bits in int
  if ((SyntaxStack0[ExprTypeSynPtr] != tokUnsigned && sr < 0) ||
      (unsigned)sr >= CHAR_BIT * sizeof(int) ||
      (unsigned)sr >= 8u * SizeOfWord)
  {
    //error("exprval(): Invalid shift count\n");
    warning("Shift count out of range\n");
    // truncate the count, so the assembler doesn't get an invalid count
    sr &= SizeOfWord * 8 - 1;
    *psr = sr;
    stack[idx][1] = sr;
  }
}

STATIC
int divCheckAndCalc(int tok, int* psl, int sr, int Unsigned, int ConstExpr[2])
{
  int div0 = 0;
  int sl = *psl;

  if (!ConstExpr[1])
    return !div0;

  if (Unsigned)
  {
    sl = (int)truncUint(sl);
    sr = (int)truncUint(sr);
  }
  else
  {
    sl = truncInt(sl);
    sr = truncInt(sr);
  }

  if (sr == 0)
  {
    div0 = 1;
  }
  else if (!ConstExpr[0])
  {
    return !div0;
  }
  else if (!Unsigned && ((sl == INT_MIN && sr == -1) || division(sl , sr) != truncInt(division(sl , sr))))
  {
    div0 = 1;
  }
  else
  {
    if (Unsigned)
    {
      if (tok == '/')
        sl = (int)((unsigned)division(sl , sr));
      else
        sl = (int)((unsigned)modulo(sl , sr));
    }
    else
    {
      // TBD!!! C89 gives freedom in how exactly division of negative integers
      // can be implemented w.r.t. rounding and w.r.t. the sign of the remainder.
      // A stricter, C99-conforming implementation, non-dependent on the
      // compiler used to compile Smaller C is needed.
      if (tok == '/')
        sl = division(sl, sr);
      else
        sl = modulo(sl, sr);
    }
    *psl = sl;
  }

  if (div0)
    warning("Division by 0 or division overflow\n");

  return !div0;
}

STATIC
void promoteType(int* ExprTypeSynPtr, int* TheOtherExprTypeSynPtr)
{
  // Integer promotion to signed int or unsigned int from smaller types
  // (all kinds of char and short). Promotion to unsigned int occurs
  // only if the other operand (of a binary operator) is already an
  // unsigned int. Effectively, this promotion to unsigned int performs
  // usual arithmetic conversion for integers.
  if (*ExprTypeSynPtr >= 0)
  {
    // chars must be promoted to ints in expressions as the very first thing
    switch (SyntaxStack0[*ExprTypeSynPtr])
    {
    case tokChar:
#ifdef CAN_COMPILE_32BIT
    case tokShort:
    case tokUShort:
#endif
    case tokSChar:
    case tokUChar:
      *ExprTypeSynPtr = SymIntSynPtr;
    }
    if (*TheOtherExprTypeSynPtr >= 0)
    {
      // ints must be converted to unsigned ints if they are used in binary
      // operators whose other operand is unsigned int (except <<,>>,<<=,>>=)
      if (SyntaxStack0[*ExprTypeSynPtr] == tokInt &&
          SyntaxStack0[*TheOtherExprTypeSynPtr] == tokUnsigned)
        *ExprTypeSynPtr = SymUintSynPtr;
    }
  }
}

STATIC
int GetFxnInfo(int ExprTypeSynPtr, int* MinParams, int* MaxParams, int* ReturnExprTypeSynPtr, int* FirstParamSynPtr)
{
  *MaxParams = *MinParams = 0;

  if (ExprTypeSynPtr < 0)
  {
    ExprTypeSynPtr = -ExprTypeSynPtr;
  }
  else
  {
    while (SyntaxStack0[ExprTypeSynPtr] == tokIdent || SyntaxStack0[ExprTypeSynPtr] == tokLocalOfs)
      ExprTypeSynPtr++;
    if (SyntaxStack0[ExprTypeSynPtr] == '*')
      ExprTypeSynPtr++;
  }

  if (SyntaxStack0[ExprTypeSynPtr] != '(')
    return 0;

  // DONE: return syntax pointer to the function's return type

  // Count params

  ExprTypeSynPtr++;

  if (FirstParamSynPtr)
    *FirstParamSynPtr = ExprTypeSynPtr;

  if (SyntaxStack0[ExprTypeSynPtr] == ')')
  {
    // "fxn()": unspecified parameters, so, there can be any number of them
    *MaxParams = 32767; // INT_MAX;
    *ReturnExprTypeSynPtr = ExprTypeSynPtr + 1;
    return 1;
  }

  if (SyntaxStack0[ExprTypeSynPtr + 1] == tokVoid)
  {
    // "fxn(void)": 0 parameters
    *ReturnExprTypeSynPtr = ExprTypeSynPtr + 3;
    return 1;
  }

  for (;;)
  {
    int tok = SyntaxStack0[ExprTypeSynPtr];

    if (tok == tokIdent)
    {
      if (SyntaxStack0[ExprTypeSynPtr + 1] != tokEllipsis)
      {
        ++*MinParams;
        ++*MaxParams;
      }
      else
      {
        *MaxParams = 32767; // INT_MAX;
      }
    }
    else if (tok == '(')
    {
      // skip parameters in parameters
      int c = 1;
      while (c && ExprTypeSynPtr < SyntaxStackCnt)
      {
        tok = SyntaxStack0[++ExprTypeSynPtr];
        c += (tok == '(') - (tok == ')');
      }
    }
    else if (tok == ')')
    {
      ExprTypeSynPtr++;
      break;
    }

    ExprTypeSynPtr++;
  }

  // get the function's return type
  *ReturnExprTypeSynPtr = ExprTypeSynPtr;

  return 1;
}

STATIC
void simplifyConstExpr(int val, int isConst, int* ExprTypeSynPtr, int top, int bottom)
{
  // If non-const, nothing to do.
  // If const and already a number behind the scenes, nothing to do
  // (val must not differ from the number!).
  if (!isConst || stack[top][0] == tokNumInt || stack[top][0] == tokNumUint)
    return;

  // Const, but not a number yet. Reduce to a number equal val.
  if (SyntaxStack0[*ExprTypeSynPtr] == tokUnsigned)
    stack[top][0] = tokNumUint;
  else
    stack[top][0] = tokNumInt;
  stack[top][1] = val;

  del(bottom, top - bottom);
}

STATIC
int AllocLocal(unsigned size)
{
  // Let's calculate variable's relative on-stack location
  int oldOfs = CurFxnLocalOfs;

  // Note: local vars are word-aligned on the stack
  CurFxnLocalOfs = (int)((CurFxnLocalOfs - size) & ~(SizeOfWord - 1u));
  if (CurFxnLocalOfs >= oldOfs ||
      CurFxnLocalOfs != truncInt(CurFxnLocalOfs) ||
      CurFxnLocalOfs < -GenMaxLocalsSize())
    //error("AllocLocal(): Local variables take too much space\n");
    errorVarSize();

  if (CurFxnMinLocalOfs > CurFxnLocalOfs)
    CurFxnMinLocalOfs = CurFxnLocalOfs;

  return CurFxnLocalOfs;
}

// DONE: sizeof(type)
// DONE: "sizeof expr"
// DONE: constant expressions
// DONE: collapse constant subexpressions into constants
STATIC
int exprval(int* idx, int* ExprTypeSynPtr, int* ConstExpr)
{
  int tok;
  int s;
  int RightExprTypeSynPtr;
  int oldIdxRight;
  int oldSpRight;
  int constExpr[3];

  if (*idx < 0)
    //error("exprval(): idx < 0\n");
    errorInternal(5);

  tok = stack[*idx][0];
  s = stack[*idx][1];

  --*idx;

  oldIdxRight = *idx;
  oldSpRight = sp;

  switch (tok)
  {
  // Constants
  case tokNumInt:
    // return the constant's type: int
    *ExprTypeSynPtr = SymIntSynPtr;
    *ConstExpr = 1;
    break;
  case tokNumUint:
    // return the constant's type: unsigned int
    *ExprTypeSynPtr = SymUintSynPtr;
    *ConstExpr = 1;
    break;
#ifndef NO_WCHAR
  case tokNumCharWide:
    // recode tokNumCharWide to tokNumInt to minimize changes in the CGs
    stack[*idx + 1][0] = tokNumInt;
    // return the constant's type: wchar_t
    *ExprTypeSynPtr = SymWideCharSynPtr;
    *ConstExpr = 1;
    break;
#endif
#ifndef NO_FP
  case tokNumFloat:
    // recode tokNumFloat to tokNumInt to minimize changes in the CGs
    stack[*idx + 1][0] = tokNumInt;
    // return the constant's type: float
    *ExprTypeSynPtr = SymFloatSynPtr;
    *ConstExpr = 1;
    break;
#endif

  // Identifiers
  case tokIdent:
    {
      // DONE: support __func__
      char* ident = IdentTable + s;
      int synPtr, type;
#ifndef NO_FUNC_
      if (CurFxnName && !strcmp(ident, "__func__"))
      {
        if (CurFxnNameLabel >= 0)
          CurFxnNameLabel = -CurFxnNameLabel;
        stack[*idx + 1][1] = SyntaxStack1[SymFuncPtr];
        synPtr = SymFuncPtr;
      }
      else
#endif
      {
        synPtr = FindSymbol(ident);
        // "Rename" static vars in function scope
        if (synPtr >= 0 && synPtr + 1 < SyntaxStackCnt && SyntaxStack0[synPtr + 1] == tokIdent)
        {
          s = stack[*idx + 1][1] = SyntaxStack1[++synPtr];
          ident = IdentTable + s;
        }
      }

      if (synPtr < 0)
      {
        if ((*idx + 2 >= sp) || stack[*idx + 2][0] != ')')
          error("Undeclared identifier '%s'\n", ident);
        else
        {
          warning("Call to undeclared function '%s()'\n", ident);
          // Implicitly declare "extern int ident();"
          PushSyntax2(tokIdent, s);
          PushSyntax('(');
          PushSyntax(')');
          PushSyntax(tokInt);
          synPtr = FindSymbol(ident);
        }
      }

#ifndef NO_TYPEDEF_ENUM
      if (synPtr + 1 < SyntaxStackCnt &&
          SyntaxStack0[synPtr + 1] == tokNumInt)
      {
        // this is an enum constant
        stack[*idx + 1][0] = tokNumInt;
        s = stack[*idx + 1][1] = SyntaxStack1[synPtr + 1];
        *ExprTypeSynPtr = SymIntSynPtr;
        *ConstExpr = 1;
        break;
      }
#endif

      // DONE: this declaration is actually a type cast
      if (!strncmp(IdentTable + SyntaxStack1[synPtr], "(something", sizeof "(something)" - 1 - 1))
      {
#ifndef NO_FP
        int fmask;
        int ptrmask;
#endif
        int castSize;

        if (SyntaxStack0[++synPtr] == tokLocalOfs) // TBD!!! is this really needed???
          synPtr++;

        s = exprval(idx, ExprTypeSynPtr, ConstExpr);

        // can't cast void or structure/union to anything (except void)
        if (*ExprTypeSynPtr >= 0 &&
            (SyntaxStack0[*ExprTypeSynPtr] == tokVoid ||
             SyntaxStack0[*ExprTypeSynPtr] == tokStructPtr) &&
            SyntaxStack0[synPtr] != tokVoid)
          errorOpType();

        // can't cast to function, array or structure/union
        if (SyntaxStack0[synPtr] == '(' ||
            SyntaxStack0[synPtr] == '[' ||
            SyntaxStack0[synPtr] == tokStructPtr)
          errorOpType();

#ifndef NO_FP
        ptrmask = isAnyPtr(synPtr) * 2 + isAnyPtr(*ExprTypeSynPtr);
        fmask = isFloat(synPtr) * 2 + isFloat(*ExprTypeSynPtr);
        if (ptrmask && fmask) // pointers and floats don't mix
          errorOpType();
#endif

        // will try to propagate constants through casts
        if (!*ConstExpr &&
            (stack[oldIdxRight - (oldSpRight - sp)][0] == tokNumInt ||
             stack[oldIdxRight - (oldSpRight - sp)][0] == tokNumUint))
        {
          s = stack[oldIdxRight - (oldSpRight - sp)][1];
          *ConstExpr = 1;
        }

        castSize = GetDeclSize(synPtr, 1); // 0 for cast to void

#ifndef NO_FP
        if (castSize && fmask == 1)
        {
          // cast from float to any int
          int u = isUint(synPtr);
          if (*ConstExpr)
          {
            s = u ? f2u(s) : f2i(s, castSize);
          }
          else
          {
            // insert a call to convert float to [unsigned] int
            int above = oldIdxRight + 1 - (oldSpRight - sp);
            int below = *idx + 1;
            ins2(above, ')', SizeOfWord);
            ins2(above, tokIdent, FindIdent(FpFxnName[u ? FXNF2U : FXNF2I]));
            ins(above, ',');
            ins2(below, '(', SizeOfWord);
          }
        }
#endif

        // insertion of tokUChar, tokSChar and tokUnaryPlus transforms
        // lvalues (values formed by dereferences) into rvalues
        // (by hiding the dereferences), just as casts should do
        switch (castSize)
        {
        case 1:
          // cast to unsigned char
          stack[oldIdxRight + 1 - (oldSpRight - sp)][0] = tokUChar;
          s &= 0xFFu;
          break;
        case -1:
          // cast to signed char
          stack[oldIdxRight + 1 - (oldSpRight - sp)][0] = tokSChar;
          if ((s &= 0xFFu) >= 0x80)
            s -= 0x100;
          break;
        default:
#ifdef CAN_COMPILE_32BIT
          if (castSize && castSize != SizeOfWord)
          {
            // cast not to void and not to word-sized type (int/unsigned/pointer/float)
            if (castSize == 2)
            {
              // cast to unsigned short
              stack[oldIdxRight + 1 - (oldSpRight - sp)][0] = tokUShort;
              s &= 0xFFFFu;
            }
            else
            {
              // cast to signed short
              stack[oldIdxRight + 1 - (oldSpRight - sp)][0] = tokShort;
              if ((s &= 0xFFFFu) >= 0x8000)
                s -= 0x10000;
            }
          }
          else // fallthrough
#endif
          {
            // cast to void or word-sized type (int/unsigned/pointer/float)
#ifndef NO_FP
            if (fmask == 2)
            {
              // cast from any int to float
              int u = isUint(*ExprTypeSynPtr);
              if (*ConstExpr)
              {
                s = u ? u2f(s) : i2f(s);
              }
              else
              {
                // insert a call to convert [unsigned] int to float
                int above = oldIdxRight + 1 - (oldSpRight - sp);
                int below = *idx + 1;
                ins2(above, ')', SizeOfWord);
                ins2(above, tokIdent, FindIdent(FpFxnName[u ? FXNU2F : FXNI2F]));
                ins(above, ',');
                ins2(below, '(', SizeOfWord);
              }
            }
#endif
            if (stack[oldIdxRight - (oldSpRight - sp)][0] == tokUnaryStar)
              // hide the dereference
              stack[oldIdxRight + 1 - (oldSpRight - sp)][0] = tokUnaryPlus;
          }
          break;
        }

        if (*ConstExpr)
          stack[oldIdxRight - (oldSpRight - sp)][1] = s;

        *ExprTypeSynPtr = synPtr;
        simplifyConstExpr(s, *ConstExpr, ExprTypeSynPtr, oldIdxRight + 1 - (oldSpRight - sp), *idx + 1);

        if (!*ConstExpr && stack[oldIdxRight + 1 - (oldSpRight - sp)][0] == tokIdent)
          // nothing to hide, remove the cast
          del(oldIdxRight + 1 - (oldSpRight - sp), 1);

        switch (SyntaxStack0[synPtr])
        {
        case tokChar:
        case tokSChar:
        case tokUChar:
#ifdef CAN_COMPILE_32BIT
        case tokShort:
        case tokUShort:
#endif
        case tokInt:
        case tokUnsigned:
#ifndef NO_FP
        case tokFloat:
#endif
          break;
        default:
          // only numeric types can be const
          *ConstExpr = 0;
          break;
        }

        break;
      }

      // Finally, not __func__, not enum, not cast.

      type = SymType(synPtr);

      if (type == SymLocalVar || type == SymLocalArr)
      {
        // replace local variables/arrays with their local addresses
        // (global variables/arrays' addresses are their names)
        stack[*idx + 1][0] = tokLocalOfs;
        stack[*idx + 1][1] = SyntaxStack1[synPtr + 1];
      }
      if (type == SymLocalVar || type == SymGlobalVar)
      {
        // add implicit dereferences for local/global variables
        ins2(*idx + 2, tokUnaryStar, GetDeclSize(synPtr, 1));
      }

      // return the identifier's type
      while (SyntaxStack0[synPtr] == tokIdent || SyntaxStack0[synPtr] == tokLocalOfs)
        synPtr++;
      *ExprTypeSynPtr = synPtr;
    }
    *ConstExpr = 0;
    break;

  // sizeof operator
  case tokSizeof:
    exprval(idx, ExprTypeSynPtr, ConstExpr);
    s = GetDeclSize(*ExprTypeSynPtr, 0);
    if (s == 0)
      error("sizeof of incomplete type\n");

    // replace sizeof with its numeric value
    stack[oldIdxRight + 1 - (oldSpRight - sp)][0] = tokNumUint;
    stack[oldIdxRight + 1 - (oldSpRight - sp)][1] = s;

    // remove the sizeof's subexpression
    del(*idx + 1, oldIdxRight - (oldSpRight - sp) - *idx);

    *ExprTypeSynPtr = SymUintSynPtr;
    *ConstExpr = 1;
    break;

  // Address unary operator
  case tokUnaryAnd:
    exprval(idx, ExprTypeSynPtr, ConstExpr);

    if (*ExprTypeSynPtr >= 0 &&
        (SyntaxStack0[*ExprTypeSynPtr] == '[' || SyntaxStack0[*ExprTypeSynPtr] == '('))
    {
      // convert an array into a pointer to the array,
      // convert a function into a pointer to the function,
      // remove the reference
      del(oldIdxRight + 1 - (oldSpRight - sp), 1);
    }
    else if (*ExprTypeSynPtr >= 0 &&
             stack[oldIdxRight - (oldSpRight - sp)][0] == tokUnaryStar)
    {
      // it's an lvalue (with implicit or explicit dereference),
      // convert it into its address by
      // collapsing/removing the reference and the dereference
      del(oldIdxRight - (oldSpRight - sp), 2);
    }
    else
      //error("exprval(): lvalue expected after '&'\n");
      errorNotLvalue();

    // we cannot insert another '*' into the type to make it a pointer
    // to an array/function/etc, so make the index into the type negative
    *ExprTypeSynPtr = -*ExprTypeSynPtr;

    *ConstExpr = 0;
    break;

  // Indirection unary operator
  case tokUnaryStar:
    exprval(idx, ExprTypeSynPtr, ConstExpr);

    if (*ExprTypeSynPtr < 0 || SyntaxStack0[*ExprTypeSynPtr] == '*')
    {
      // type is a pointer to something,
      // transform it into that something
      if (*ExprTypeSynPtr < 0)
        *ExprTypeSynPtr = -*ExprTypeSynPtr;
      else
        ++*ExprTypeSynPtr;
      nonVoidTypeCheck(*ExprTypeSynPtr);
      if (SyntaxStack0[*ExprTypeSynPtr] == tokStructPtr && !GetDeclSize(*ExprTypeSynPtr, 0))
        // incomplete structure/union type
        errorOpType();
      // remove the dereference if that something is an array or a function
      if (SyntaxStack0[*ExprTypeSynPtr] == '[' ||
          SyntaxStack0[*ExprTypeSynPtr] == '(')
        del(oldIdxRight + 1 - (oldSpRight - sp), 1);
      // else attach dereference size in bytes
      else
        stack[oldIdxRight + 1 - (oldSpRight - sp)][1] = GetDeclSize(*ExprTypeSynPtr, 1);
    }
    else if (SyntaxStack0[*ExprTypeSynPtr] == '[')
    {
      // type is an array,
      // transform it into the array's first element
      // (a subarray, if type is a multidimensional array)
      (*ExprTypeSynPtr) += 3;
      // remove the dereference if that element is an array
      if (SyntaxStack0[*ExprTypeSynPtr] == '[')
        del(oldIdxRight + 1 - (oldSpRight - sp), 1);
      // else attach dereference size in bytes
      else
        stack[oldIdxRight + 1 - (oldSpRight - sp)][1] = GetDeclSize(*ExprTypeSynPtr, 1);
    }
    else
      //error("exprval(): pointer/array expected after '*' / before '[]'\n");
      errorOpType();

    *ConstExpr = 0;
    break;

  // Additive binary operators
  case '+':
  case '-':
  // WRONGISH: DONE: replace prefix ++/-- with +=1/-=1
  // WRONG: DONE: replace postfix ++/-- with (+=1)-1/(-=1)+1
    {
      int ptrmask;
#ifndef NO_FP
      int fmask;
#endif
      int oldIdxLeft, oldSpLeft;
      int sl, sr;
      int incSize;
      sr = exprval(idx, &RightExprTypeSynPtr, &constExpr[1]);
      oldIdxLeft = *idx;
      oldSpLeft = sp;
      sl = exprval(idx, ExprTypeSynPtr, &constExpr[0]);

      // Decay arrays to pointers to their first elements
      // and ensure that the pointers are suitable for pointer arithmetic
      // (not pointers to functions, sizes of pointees are known and non-zero)
      decayArray(&RightExprTypeSynPtr, 1);
      decayArray(ExprTypeSynPtr, 1);

      // Bar void and struct/union
      scalarTypeCheck(RightExprTypeSynPtr);
      scalarTypeCheck(*ExprTypeSynPtr);

      ptrmask = isAnyPtr(RightExprTypeSynPtr) + isAnyPtr(*ExprTypeSynPtr) * 2;
#ifndef NO_FP
      fmask = isFloat(RightExprTypeSynPtr) + isFloat(*ExprTypeSynPtr) * 2;
      if (ptrmask && fmask) // pointers and floats don't mix
        errorOpType();
#endif

      // DONE: index/subscript scaling
      if (ptrmask == 1 && tok == '+') // pointer in right-hand expression
      {
        incSize = GetDeclSize(derefAnyPtr(RightExprTypeSynPtr), 0);

        if (constExpr[0]) // integer constant in left-hand expression
        {
          s = (int)((unsigned)sl * incSize);
          stack[oldIdxLeft - (oldSpLeft - sp)][1] = s;
          // optimize a little if possible
          {
            int i = oldIdxRight - (oldSpRight - sp);
            // Skip any type cast markers
            while (stack[i][0] == tokUnaryPlus || stack[i][0] == '+')
              i--;
            // See if the pointer is an integer constant or a local variable offset
            // and if it is, adjust it here instead of generating code for
            // addition/subtraction
            if (stack[i][0] == tokNumInt || stack[i][0] == tokNumUint || stack[i][0] == tokLocalOfs)
            {
              s = (int)((unsigned)stack[i][1] + s);
              stack[i][1] = s; // TBD!!! need extra truncation?
              del(oldIdxLeft - (oldSpLeft - sp), 1);
              del(oldIdxRight - (oldSpRight - sp) + 1, 1);
            }
          }
        }
        else if (incSize != 1)
        {
          ins2(oldIdxLeft + 1 - (oldSpLeft - sp), tokNumInt, incSize);
          ins(oldIdxLeft + 1 - (oldSpLeft - sp), '*');
        }

        *ExprTypeSynPtr = RightExprTypeSynPtr;
      }
      else if (ptrmask == 2) // pointer in left-hand expression
      {
        incSize = GetDeclSize(derefAnyPtr(*ExprTypeSynPtr), 0);
        if (constExpr[1]) // integer constant in right-hand expression
        {
          s = (int)((unsigned)sr * incSize);
          stack[oldIdxRight - (oldSpRight - sp)][1] = s;
          // optimize a little if possible
          {
            int i = oldIdxLeft - (oldSpLeft - sp);
            // Skip any type cast markers
            while (stack[i][0] == tokUnaryPlus || stack[i][0] == '+')
              i--;
            // See if the pointer is an integer constant or a local variable offset
            // and if it is, adjust it here instead of generating code for
            // addition/subtraction
            if (stack[i][0] == tokNumInt || stack[i][0] == tokNumUint || stack[i][0] == tokLocalOfs)
            {
              if (tok == '-')
                s = (int)~(s - 1u);
              s = (int)((unsigned)stack[i][1] + s);
              stack[i][1] = s; // TBD!!! need extra truncation?
              del(oldIdxRight - (oldSpRight - sp), 2);
            }
          }
        }
        else if (incSize != 1)
        {
          ins2(oldIdxRight + 1 - (oldSpRight - sp), tokNumInt, incSize);
          ins(oldIdxRight + 1 - (oldSpRight - sp), '*');
        }
      }
      else if (ptrmask == 3 && tok == '-') // pointers in both expressions
      {
        incSize = GetDeclSize(derefAnyPtr(*ExprTypeSynPtr), 0);
        // TBD!!! "ptr1-ptr2": better pointer type compatibility test needed, like compatCheck()?
        if (incSize != GetDeclSize(derefAnyPtr(RightExprTypeSynPtr), 0))
          //error("exprval(): incompatible pointers\n");
          errorOpType();
        if (incSize != 1)
        {
          ins2(oldIdxRight + 2 - (oldSpRight - sp), tokNumInt, incSize);
          ins(oldIdxRight + 2 - (oldSpRight - sp), '/');
        }
        *ExprTypeSynPtr = SymIntSynPtr;
      }
      else if (ptrmask)
        //error("exprval(): invalid combination of operands for '+' or '-'\n");
        errorOpType();

      // Promote the result from char to int (and from int to unsigned) if necessary
      promoteType(ExprTypeSynPtr, &RightExprTypeSynPtr);

      *ConstExpr = constExpr[0] && constExpr[1];

#ifndef NO_FP
      if (fmask)
      {
        if (fmask == 2)
        {
          int u = isUint(RightExprTypeSynPtr);
          if (constExpr[1])
          {
            // convert int constant to float
            sr = u ? u2f(sr) : i2f(sr);
            stack[oldIdxRight - (oldSpRight - sp)][1] = sr;
          }
          else
          {
            // insert a call to convert int to float
            int above = oldIdxRight + 1 - (oldSpRight - sp);
            int below = oldIdxLeft + 1 - (oldSpLeft - sp);
            ins2(above, ')', SizeOfWord);
            ins2(above, tokIdent, FindIdent(FpFxnName[u ? FXNU2F : FXNI2F]));
            ins(above, ',');
            ins2(below, '(', SizeOfWord);
            oldSpLeft += 4;
          }
        }
        if (fmask == 1)
        {
          int u = isUint(*ExprTypeSynPtr);
          if (constExpr[0])
          {
            // convert int constant to float
            sl = u ? u2f(sl) : i2f(sl);
            stack[oldIdxLeft - (oldSpLeft - sp)][1] = sl;
          }
          else
          {
            // insert a call to convert int to float
            int above = oldIdxLeft + 1 - (oldSpLeft - sp);
            int below = *idx + 1;
            ins2(above, ')', SizeOfWord);
            ins2(above, tokIdent, FindIdent(FpFxnName[u ? FXNU2F : FXNI2F]));
            ins(above, ',');
            ins2(below, '(', SizeOfWord);
          }
        }
        if (*ConstExpr)
        {
          if (tok == '+')
            s = fadd(sl, sr);
          else
            s = fsub(sl, sr);
        }
        else
        {
          // insert a call to add/subtract floats
          int above = oldIdxRight + 1 - (oldSpRight - sp);
          int mid = oldIdxLeft + 1 - (oldSpLeft - sp);
          int below = *idx + 1;
          if (tok == '-')
          {
            // minuend must be the first argument, swap
            swap(below, mid - below, above - mid);
            mid = above - mid + below;
          }
          stack[above][0] = ')'; // replace '+'/'-' with function call
          stack[above][1] = SizeOfWord * 2;
          ins2(above, tokIdent, FindIdent(FpFxnName[(tok == '+') ? FXNFADD : FXNFSUB]));
          ins(above, ',');
          ins(mid, ',');
          ins2(below, '(', SizeOfWord * 2);
        }
        *ExprTypeSynPtr = SymFloatSynPtr;
      }
      else
#endif
      {
        if (tok == '+')
          s = (int)((unsigned)sl + sr);
        else
          s = (int)((unsigned)sl - sr);
      }

      simplifyConstExpr(s, *ConstExpr, ExprTypeSynPtr, oldIdxRight + 1 - (oldSpRight - sp), *idx + 1);
    }
    break;

  // Prefix/postfix increment/decrement unary operators
  case tokInc:
  case tokDec:
  case tokPostInc:
  case tokPostDec:
    {
      int incSize = 1;
      int inc = tok == tokInc || tok == tokPostInc;
      int post = tok == tokPostInc || tok == tokPostDec;
      int opSize;

      exprval(idx, ExprTypeSynPtr, ConstExpr);

      lvalueCheck(*ExprTypeSynPtr, oldIdxRight - (oldSpRight - sp));

      // if it's a pointer, ensure that it's suitable for pointer arithmetic
      // (not pointer to function, pointee size is known and non-zero)
      decayArray(ExprTypeSynPtr, 1); // no actual decay here, just a type check

      // Bar void and struct/union
      scalarTypeCheck(*ExprTypeSynPtr);

#ifndef NO_FP
      // TBD!!! support floats with these operators
      if (isFloat(*ExprTypeSynPtr))
        error("Increment/decrement not supported with floats\n");
#endif

      // "remove" the lvalue dereference as we don't need
      // to read the value while forgetting its location.
      // We need to keep the lvalue location.
      // Remember the operand size.
      opSize = stack[oldIdxRight - (oldSpRight - sp)][1];
      del(oldIdxRight - (oldSpRight - sp), 1);

      if (isAnyPtr(*ExprTypeSynPtr))
        incSize = GetDeclSize(derefAnyPtr(*ExprTypeSynPtr), 0);

      if (incSize == 1)
      {
        // store the operand size in the operator
        stack[oldIdxRight + 1 - (oldSpRight - sp)][1] = opSize;
      }
      else
      {
        // replace ++/-- with "postfix" +=/-= incSize when incSize != 1
        stack[oldIdxRight + 1 - (oldSpRight - sp)][0] =
          inc ? (post ? tokPostAdd : tokAssignAdd) :
                (post ? tokPostSub : tokAssignSub);
        // store the operand size in the operator
        stack[oldIdxRight + 1 - (oldSpRight - sp)][1] = opSize;
        ins2(oldIdxRight + 1 - (oldSpRight - sp), tokNumInt, incSize);
      }

      *ConstExpr = 0;
    }
    break;

  // Simple assignment binary operator
  case '=':
    {
      int oldIdxLeft, oldSpLeft;
      int opSize;
      int structs;
#ifndef NO_FP
      int ptrmask;
      int fmask;
      int sr =
#endif
        exprval(idx, &RightExprTypeSynPtr, &constExpr[1]);
      oldIdxLeft = *idx;
      oldSpLeft = sp;
      exprval(idx, ExprTypeSynPtr, &constExpr[0]);

      lvalueCheck(*ExprTypeSynPtr, oldIdxLeft - (oldSpLeft - sp));

      nonVoidTypeCheck(RightExprTypeSynPtr);
      nonVoidTypeCheck(*ExprTypeSynPtr);

      structs = (*ExprTypeSynPtr >= 0 && SyntaxStack0[*ExprTypeSynPtr] == tokStructPtr) * 2 +
                (RightExprTypeSynPtr >= 0 && SyntaxStack0[RightExprTypeSynPtr] == tokStructPtr);
#ifndef NO_FP
      ptrmask = isAnyPtr(*ExprTypeSynPtr) * 2 + isAnyPtr(RightExprTypeSynPtr);
      fmask = isFloat(*ExprTypeSynPtr) * 2 + isFloat(RightExprTypeSynPtr);
      if (fmask && (structs | ptrmask)) // floats don't mix with pointers or structs/unions
        errorOpType();
#endif

      if (structs)
      {
        int sz;

        if (structs != 3 ||
            SyntaxStack1[RightExprTypeSynPtr] != SyntaxStack1[*ExprTypeSynPtr])
          errorOpType();

        // TBD??? (a = b) should be an rvalue and so &(a = b) and (&(a = b))->c shouldn't be
        // allowed, while (a = b).c should be allowed.

        // transform "*psleft = *psright" into "*fxn(sizeof *psright, psright, psleft)"
/*
        if (stack[oldIdxLeft - (oldSpLeft - sp)][0] != tokUnaryStar ||
            stack[oldIdxRight - (oldSpRight - sp)][0] != tokUnaryStar)
          errorInternal(18);
*/
        stack[oldIdxLeft - (oldSpLeft - sp)][0] = ','; // replace '*' with ','
        stack[oldIdxRight - (oldSpRight - sp)][0] = ','; // replace '*' with ','

        sz = GetDeclSize(RightExprTypeSynPtr, 0);

        stack[oldIdxRight + 1 - (oldSpRight - sp)][0] = tokNumUint; // replace '=' with "sizeof *psright"
        stack[oldIdxRight + 1 - (oldSpRight - sp)][1] = sz;

        ins(oldIdxRight + 2 - (oldSpRight - sp), ',');

        if (!StructCpyLabel)
          StructCpyLabel = LabelCnt++;
        ins2(oldIdxRight + 2 - (oldSpRight - sp), tokIdent, AddNumericIdent(StructCpyLabel));

        ins2(oldIdxRight + 2 - (oldSpRight - sp), ')', SizeOfWord * 3);
        ins2(oldIdxRight + 2 - (oldSpRight - sp), tokUnaryStar, 0); // use 0 deref size to drop meaningless dereferences

        ins2(*idx + 1, '(', SizeOfWord * 3);
      }
      else
      {
#ifndef NO_FP
        if (fmask == 1 || fmask == 2)
        {
          int u = isUint((fmask == 1) ? *ExprTypeSynPtr : RightExprTypeSynPtr);
          if (constExpr[1])
          {
            // convert between float and [unsigned] int
            if (fmask == 1)
              sr = u ? f2u(sr) : f2i(sr, GetDeclSize(*ExprTypeSynPtr, 1));
            else
              sr = u ? u2f(sr) : i2f(sr);
            stack[oldIdxRight - (oldSpRight - sp)][1] = sr;
          }
          else
          {
            // insert a call to convert between float and [unsigned] int
            int above = oldIdxRight + 1 - (oldSpRight - sp);
            int below = oldIdxLeft + 1 - (oldSpLeft - sp);
            ins2(above, ')', SizeOfWord);
            ins2(above, tokIdent, FindIdent(FpFxnName[(fmask == 1) ? (u ? FXNF2U : FXNF2I) :
                                                                     (u ? FXNU2F : FXNI2F)]));
            ins(above, ',');
            ins2(below, '(', SizeOfWord);
            oldSpLeft += 4;
          }
        }
#endif
        // "remove" the lvalue dereference as we don't need
        // to read the value while forgetting its location.
        // We need to keep the lvalue location.
        // Remember the operand size.
        opSize = stack[oldIdxLeft - (oldSpLeft - sp)][1];
        // store the operand size in the operator
        stack[oldIdxRight + 1 - (oldSpRight - sp)][1] = opSize;
        del(oldIdxLeft - (oldSpLeft - sp), 1);
      }

      *ConstExpr = 0;
    }
    break;

  // DONE: other assignment operators

  // Arithmetic and bitwise unary operators
  case '~':
  case tokUnaryPlus:
  case tokUnaryMinus:
    s = exprval(idx, ExprTypeSynPtr, ConstExpr);
    numericTypeCheck(*ExprTypeSynPtr);
    promoteType(ExprTypeSynPtr, ExprTypeSynPtr);
    switch (tok)
    {
    case '~':
#ifndef NO_FP
      nonFloatTypeCheck(*ExprTypeSynPtr);
#endif
      s = ~s;
      break;
    case tokUnaryPlus:
      break;
    case tokUnaryMinus:
#ifndef NO_FP
      if (isFloat(*ExprTypeSynPtr))
      {
        if (*ConstExpr)
        {
          s = fneg(s);
        }
        else
        {
          // insert a call to float negate
          int above = oldIdxRight + 1 - (oldSpRight - sp);
          int below = *idx + 1;
          stack[above][0] = ')'; // replace tokUnaryMinus with function call
          stack[above][1] = SizeOfWord;
          ins2(above, tokIdent, FindIdent(FpFxnName[FXNFNEG]));
          ins(above, ',');
          ins2(below, '(', SizeOfWord);
        }
      }
      else
#endif
      {
        s = (int)~(s - 1u);
      }
      break;
    }
    simplifyConstExpr(s, *ConstExpr, ExprTypeSynPtr, oldIdxRight + 1 - (oldSpRight - sp), *idx + 1);
    break;

  // Arithmetic and bitwise binary operators
  case '*':
  case '/':
  case '%':
  case tokLShift:
  case tokRShift:
  case '&':
  case '^':
  case '|':
    {
#ifndef NO_FP
      int fmask;
      int oldIdxLeft, oldSpLeft;
#endif
      int sr, sl;
      int Unsigned;
      sr = exprval(idx, &RightExprTypeSynPtr, &constExpr[1]);
#ifndef NO_FP
      oldIdxLeft = *idx;
      oldSpLeft = sp;
#endif
      sl = exprval(idx, ExprTypeSynPtr, &constExpr[0]);

      numericTypeCheck(RightExprTypeSynPtr);
      numericTypeCheck(*ExprTypeSynPtr);
#ifndef NO_FP
      if (tok != '*' && tok != '/')
      {
        nonFloatTypeCheck(RightExprTypeSynPtr);
        nonFloatTypeCheck(*ExprTypeSynPtr);
      }
#endif

      *ConstExpr = constExpr[0] && constExpr[1];

      Unsigned = SyntaxStack0[*ExprTypeSynPtr] == tokUnsigned || SyntaxStack0[RightExprTypeSynPtr] == tokUnsigned;
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
