bartpleiter/FPGC5/Assembler/BDOSshivyC.asm

; This file is used to look up how certain things were done by the shivyC compiler (for when I'm confused with SmallerC)
; Setup stack and return function before jumping to Main of C program
Main:
    load32 0x77FFFF rsp     ; initialize (BDOS) main stack address
    addr2reg Return_UART r1 ; get address of return function
    sub r1 4 r1             ; remove 4 from address, since function return has offset 4
    write 0 rsp r1          ; write return address on stack
    jump Label_main         ; jump to main of C program
                            ; should return to the address we just put on the stack
    halt                    ; should not get here

; Function that is called after Main of C program has returned
; Return value should be in R1
; Send it over UART and halt afterwards
Return_UART:
    load32 0xC02723 r2          ; r2 = 0xC02723 | UART tx
    write 0 r2 r1               ; write r1 over UART
    halt                        ; halt

; COMPILED C CODE HERE

Label_UserprogramRunning:
	.dw 0
Label_timer1Value:
	.dw 0
Label_timer2Value:
	.dw 0
Label_timer3Value:
	.dw 0
Label_GFX_cursor:
	.dw 0
Label_hidfifo:
	.dw 0 0 0 0 0 0 0 0 0 0 0 0 0 0 0 0 0 0 0 0 0 0 0 0 0 0 0 0 0 0 0 0
Label_hidreadIdx:
	.dw 0
Label_hidwriteIdx:
	.dw 0
Label_hidbufSize:
	.dw 0
Label_ps2caps:
	.dw 0
Label_ps2shifted:
	.dw 0
Label_ps2controlled:
	.dw 0
Label_ps2alted:
	.dw 0
Label_ps2extended:
	.dw 0
Label_ps2released:
	.dw 0
Label_USBkeyboard_endp_mode:
	.dw 128
Label_USBkeyboard_buffer:
	.dw 0 0 0 0 0 0 0 0
Label_USBkeyboard_buffer_prev:
	.dw 0 0 0 0 0 0 0 0
Label_USBkeyboard_holdCounter:
	.dw 0
Label_USBkeyboard_holdButton:
	.dw 0
Label_NETLOADER_transferState:
	.dw 0
Label_NETLOADER_wordPosition:
	.dw 0
Label_NETLOADER_currentByteShift:
	.dw 24
Label_SHELL_commandIdx:
	.dw 0
Label_SHELL_promptCursorPos:
	.dw 0
Label___strlit1437:
	.dw 10 0
Label___strlit1438:
	.dw 10 0
Label___strlit1439:
	.dw 10 0
Label___strlit1440:
	.dw 10 0
Label___strlit1441:
	.dw 10 0
Label___strlit1442:
	.dw 69 58 32 69 114 114 111 114 32 119 104 105 108 101 32 114 101 97 100 105 110 103 32 100 97 116 97 0
Label___strlit1443:
	.dw 69 58 32 69 114 114 111 114 32 119 104 105 108 101 32 119 114 105 116 105 110 103 32 100 97 116 97 0
Label___strlit1444:
	.dw 47 0
Label___strlit1445:
	.dw 70 65 84 115 116 114 105 110 103 58 32 76 101 110 32 97 114 103 117 109 101 110 116 32 62 32 56 0
Label___strlit1446:
	.dw 85 110 101 120 112 101 99 116 101 100 32 70 65 84 32 116 97 98 108 101 32 108 101 110 103 116 104 0
Label___strlit1447:
	.dw 46 32 32 32 32 32 32 32 32 32 32 0
Label___strlit1448:
	.dw 46 46 32 32 32 32 32 32 32 32 32 0
Label___strlit1449:
	.dw 42 0
Label___strlit1450:
	.dw 47 0
Label___strlit1451:
	.dw 47 0
Label___strlit1452:
	.dw 69 58 32 72 73 68 32 66 117 102 102 101 114 32 102 117 108 108 0
Label___strlit1453:
	.dw 69 58 32 72 73 68 32 66 117 102 102 101 114 32 101 109 112 116 121 0
Label___strlit1454:
	.dw 78 69 87 10 0
Label___strlit1455:
	.dw 85 83 66 10 0
Label___strlit1456:
	.dw 68 65 84 10 0
Label___strlit1457:
	.dw 69 78 68 10 0
Label___strlit1458:
	.dw 68 65 84 10 0
Label___strlit1459:
	.dw 69 78 68 10 0
Label___strlit1460:
	.dw 69 82 82 79 82 0
Label___strlit1461:
	.dw 68 79 78 69 0
Label___strlit1462:
	.dw 62 32 0
Label___strlit1463:
	.dw 69 58 32 73 110 118 97 108 105 100 32 112 97 116 104 10 0
Label___strlit1464:
	.dw 47 66 73 78 47 0
Label___strlit1465:
	.dw 76 111 97 100 105 110 103 32 112 114 111 103 114 97 109 0
Label___strlit1466:
	.dw 87 58 32 69 114 114 111 114 32 114 101 97 100 105 110 103 32 102 105 108 101 10 0
Label___strlit1467:
	.dw 100 111 110 101 33 10 0
Label___strlit1468:
	.dw 69 58 32 67 111 117 108 100 32 110 111 116 32 109 111 118 101 32 116 111 32 115 116 97 114 116 32 111 102 32 102 105 108 101 10 0
Label___strlit1469:
	.dw 69 58 32 80 114 111 103 114 97 109 32 105 115 32 116 111 111 32 108 97 114 103 101 10 0
Label___strlit1470:
	.dw 69 58 32 85 110 107 110 111 119 110 32 99 111 109 109 97 110 100 10 0
Label___strlit1471:
	.dw 69 58 32 67 111 117 108 100 32 110 111 116 32 111 112 101 110 32 102 105 108 101 10 0
Label___strlit1472:
	.dw 69 58 32 85 110 107 110 111 119 110 32 99 111 109 109 97 110 100 10 0
Label___strlit1473:
	.dw 69 58 32 73 110 118 97 108 105 100 32 112 97 116 104 10 0
Label___strlit1474:
	.dw 87 58 32 69 114 114 111 114 32 114 101 97 100 105 110 103 32 102 105 108 101 10 0
Label___strlit1475:
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
	.dw 0b00001111111100000000001111000000
	.dw 0b00000000000000000000000000000000
	.dw 0b00000000000000000000000000000000
	.dw 0b00000000000000000000000000000000
	.dw 0b00000000000000000000000000000000
	.dw 0b00000000000000000000000000000000
	.dw 0b00001111000000000011111111000000
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
